ealegremendoza/proyecto_4to/docs/modulos/acc/acelerometro que consigio lucas.jpg

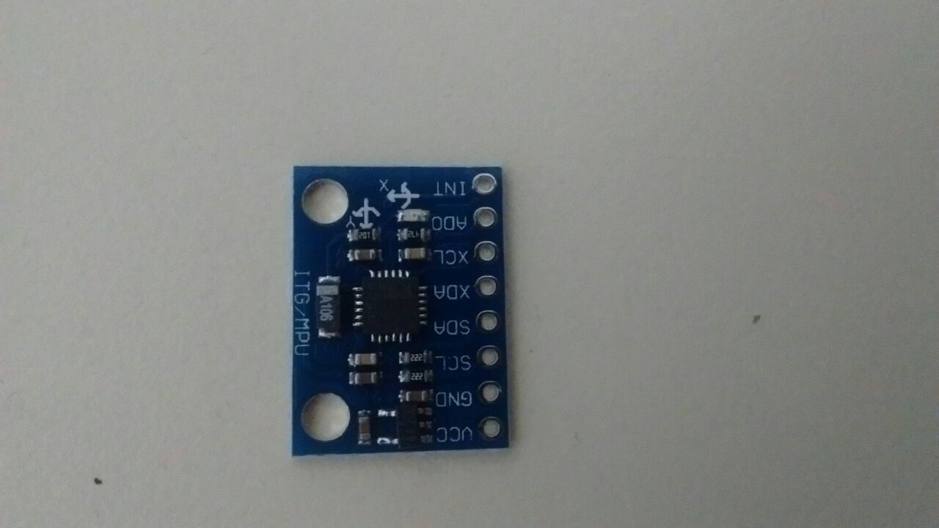
docs/modulos/acc/acelerometro que consigio lucas.jpg
