ealegremendoza/proyecto_4to/ezequiel/lpc1769_footprints.png

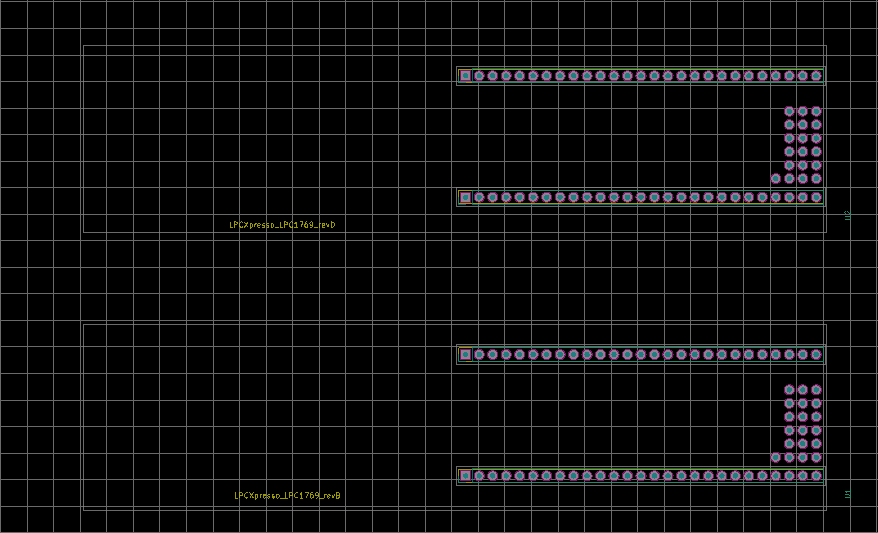
ezequiel/lpc1769_footprints.png
