ealegremendoza/proyecto_4to/docs/lpc_info/potencia_proyecto_lpc.ods

Periférico | Condición | Valor típico de suministro de corriente a 100MHz – [mA] | Notas | Vmax | Pmax | Cantidad | Pmaxtotal
Timer |  | 0,23 | Average current per timer |  | 0 | 2 | 0
UART |  | 0,53 | Average current per timer |  | 0 | 1 | 0
I2C |  | 0,16 | Average current per I2C | 0,7 | 0,112 | 1 | 0,112
SSP1 |  | 0,32 |  |  | 0 | 3 | 0
GPIO |  | 2,58 |  | 0,99 | 2,5542 | 10 | 25,542
PLL |  | CUANTO CONSUME? |  |  | #VALOR! | 1 | #VALOR!
