ealegremendoza/proyecto_4to/docs/gantt/gant_proy4to_planner_v1.pdf

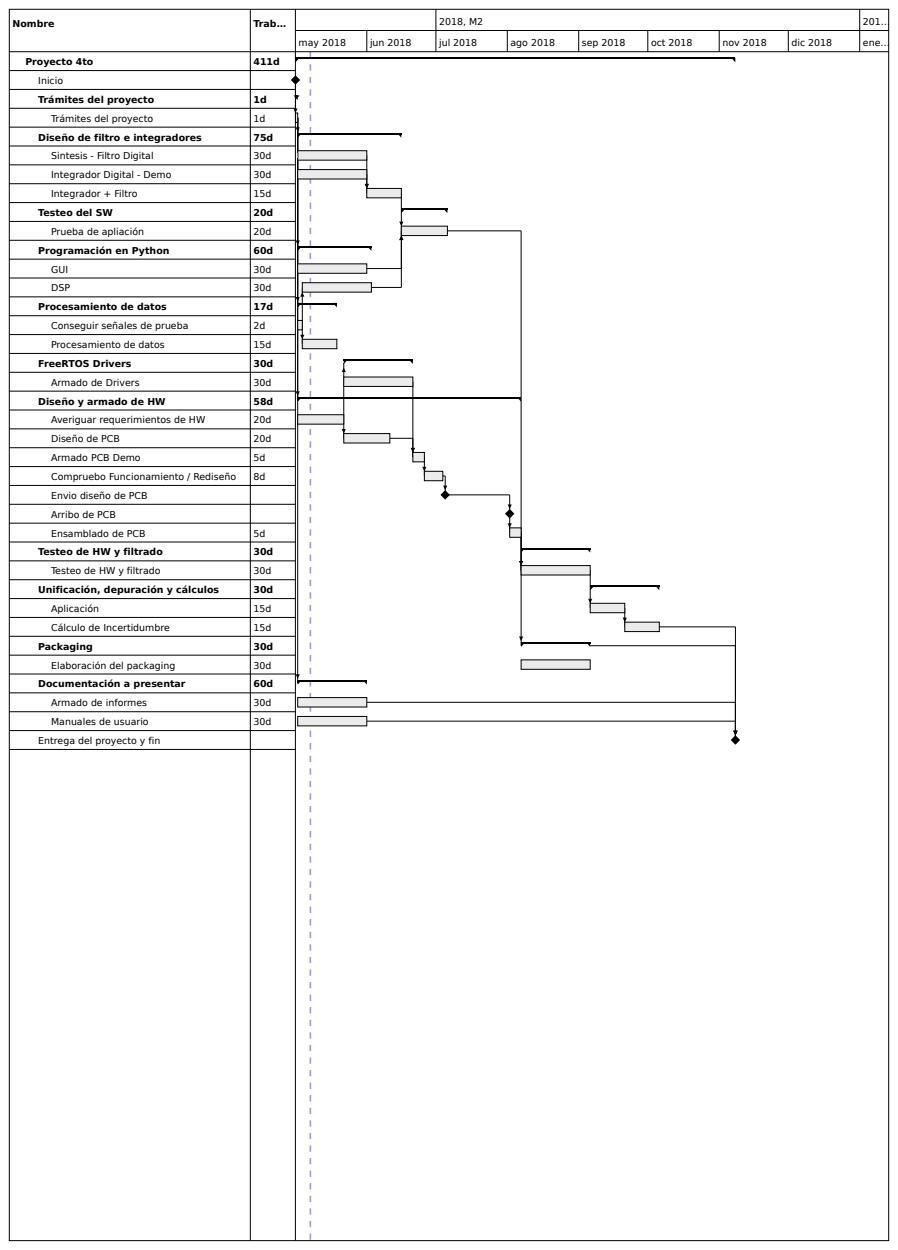
[picture p51: page 1]
Proyecto 4to; Trámites del proyecto; Diseño de filtro e integradores; Sintesis - Filtro Digital; Integrador Digital - Demo; Integrador + Filtro; Testeo del SW; Prueba de apliación; Programación en Python; GUI; DSP; Procesamiento de datos; Conseguir señales de prueba; FreeRTOS Drivers; Armado de Drivers; Diseño y armado de HW; Averiguar requerimientos de HW; Diseño de PCB; Armado PCB Demo; Compruebo Funcionamiento / Rediseño; Ensamblado de PCB; Testeo de HW y filtrado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

Inicio
Envio diseño de PCB
Arribo de PCB
Entrega del proyecto y fin

WBS | Nombre | Inicio | Fin | Trabajo | Duración | Desperdicio | Coste | Asignado a | % Completado
1 | Proyecto 4to | may 1 | nov 8 | 411d | 191d | | 0 | | 0
1.1 | Inicio | may 1 | may 1 | N/D | N/D | 62d | 0 | | 0
1.2 | Trámites del proyecto | may 1 | may 1 | 1d | 22h 58min | 190d | 0 | | 0
1.2.1 | Trámites del proyecto | may 1 | may 1 | 1d | 1d | 62d | 0 | | 0
1.3 | Diseño de filtro e integradores | may 1 | jun 15 | 75d | 45d | 145d | 0 | | 0
1.3.1 | Sintesis - Filtro Digital | may 1 | may 31 | 30d | 30d | 65d | 0 | | 2
1.3.2 | Integrador Digital - Demo | may 1 | may 31 | 30d | 30d | 65d | 0 | | 0
1.3.3 | Integrador + Filtro | may 31 | jun 15 | 15d | 15d | 65d | 0 | | 0
1.4 | Testeo del SW | jun 15 | jul 5 | 20d | 20d | 125d | 0 | | 0
1.4.1 | Prueba de apliación | jun 15 | jul 5 | 20d | 20d | 65d | 0 | | 0
1.5 | Programación en Python | may 1 | jun 2 | 60d | 32d | 158d | 0 | | 0
1.5.1 | GUI | may 1 | may 31 | 30d | 30d | 80d | 0 | | 0
1.5.2 | DSP | may 3 | jun 2 | 30d | 30d | 78d | 0 | | 0
1.6 | Procesamiento de datos | may 1 | may 18 | 17d | 17d | 173d | 0 | | 0
1.6.1 | Conseguir señales de prueba | may 1 | may 3 | 2d | 2d | 78d | 0 | | 0
1.6.2 | Procesamiento de datos | may 3 | may 18 | 15d | 15d | 173d | 0 | | 0
1.7 | FreeRTOS Drivers | may 21 | jun 20 | 30d | 30d | 140d | 0 | | 0
1.7.1 | Armado de Drivers | may 21 | jun 20 | 30d | 30d | 62d | 0 | | 0
1.8 | Diseño y armado de HW | may 1 | ago 6 | 58d | 97d | 93d | 0 | | 0
1.8.1 | Averiguar requerimientos de HW | may 1 | may 21 | 20d | 20d | 62d | 0 | | 0
1.8.2 | Diseño de PCB | may 21 | jun 10 | 20d | 20d | 72d | 0 | | 0
1.8.3 | Armado PCB Demo | jun 20 | jun 25 | 5d | 5d | 62d | 0 | | 0
1.8.4 | Compruebo Funcionamiento / Rediseño | jun 25 | jul 3 | 8d | 8d | 62d | 0 | | 0
1.8.5 | Envio diseño de PCB | jul 5 | jul 5 | N/D | N/D | 61d | 0 | | 0
1.8.6 | Arribo de PCB | ago 2 | ago 2 | N/D | N/D | 33d | 0 | | 0
1.8.7 | Ensamblado de PCB | ago 2 | ago 6 | 5d | 5d | 33d | 0 | | 0
1.9 | Testeo de HW y filtrado | ago 6 | sep 5 | 30d | 30d | 63d | 0 | | 0
1.9.1 | Testeo de HW y filtrado | ago 6 | sep 5 | 30d | 30d | 33d | 0 | | 0
1.10 | Unificación, depuración y cálculos | sep 5 | oct 5 | 30d | 30d | 33d | 0 | | 0
1.10.1 | Aplicación | sep 5 | sep 20 | 15d | 15d | 33d | 0 | | 0
1.10.2 | Cálculo de Incertidumbre | sep 20 | oct 5 | 15d | 15d | 33d | 0 | | 0
1.11 | Packaging | ago 6 | sep 5 | 30d | 30d | 63d | 0 | | 0
1.11.1 | Elaboración del packaging | ago 6 | sep 5 | 30d | 30d | 63d | 0 | | 0
1.12 | Documentación a presentar | may 1 | may 31 | 60d | 30d | 160d | 0 | | 0
1.12.1 | Armado de informes | may 1 | may 31 | 30d | 30d | 160d | 0 | | 0
1.12.2 | Manuales de usuario | may 1 | may 31 | 30d | 30d | 160d | 0 | | 0
1.13 | Entrega del proyecto y fin | nov 8 | nov 8 | N/D | N/D | | 0 | | 0
