ealegremendoza/proyecto_4to/pcbs/cargador/pdf/cargador_pcb_1.pdf

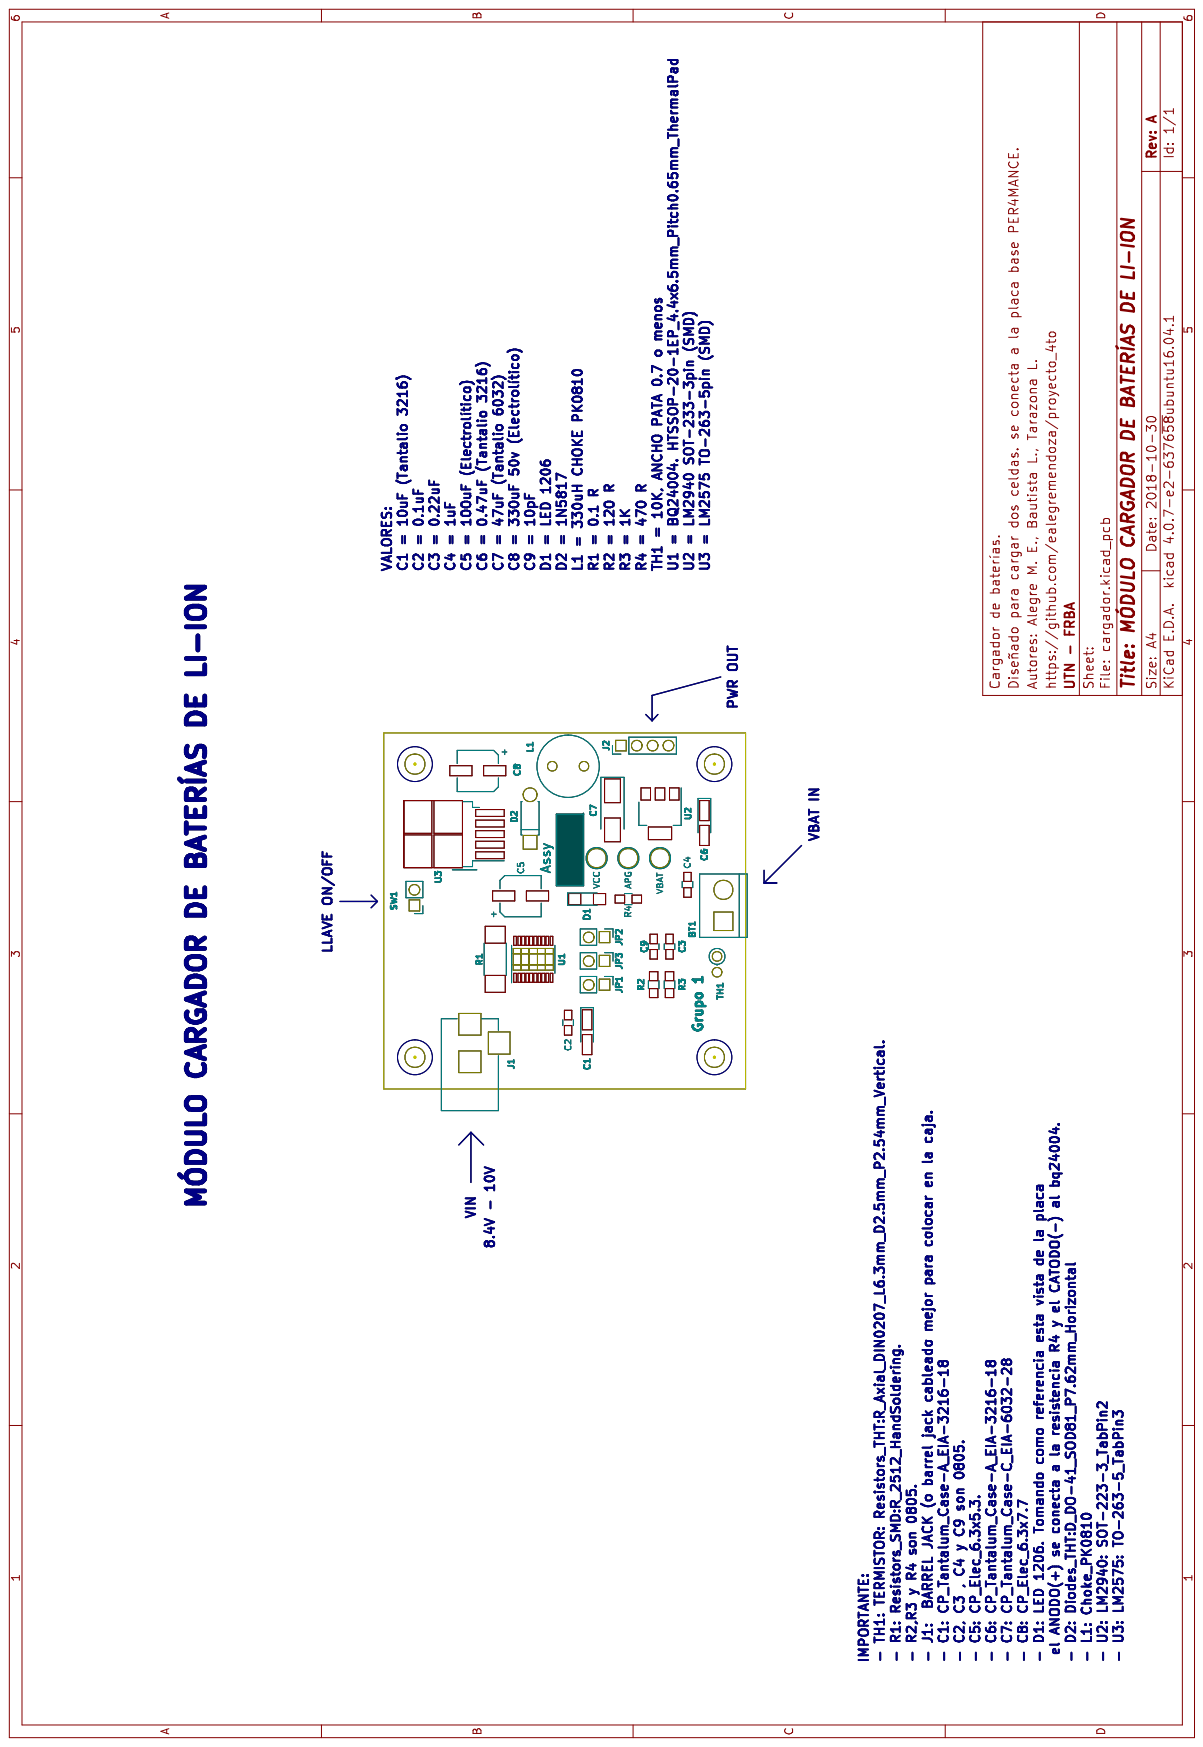
[picture p52: page 1]
