ealegremendoza/proyecto_4to/pcbs/cargador/pdf/cargador_pcb_bottom.pdf

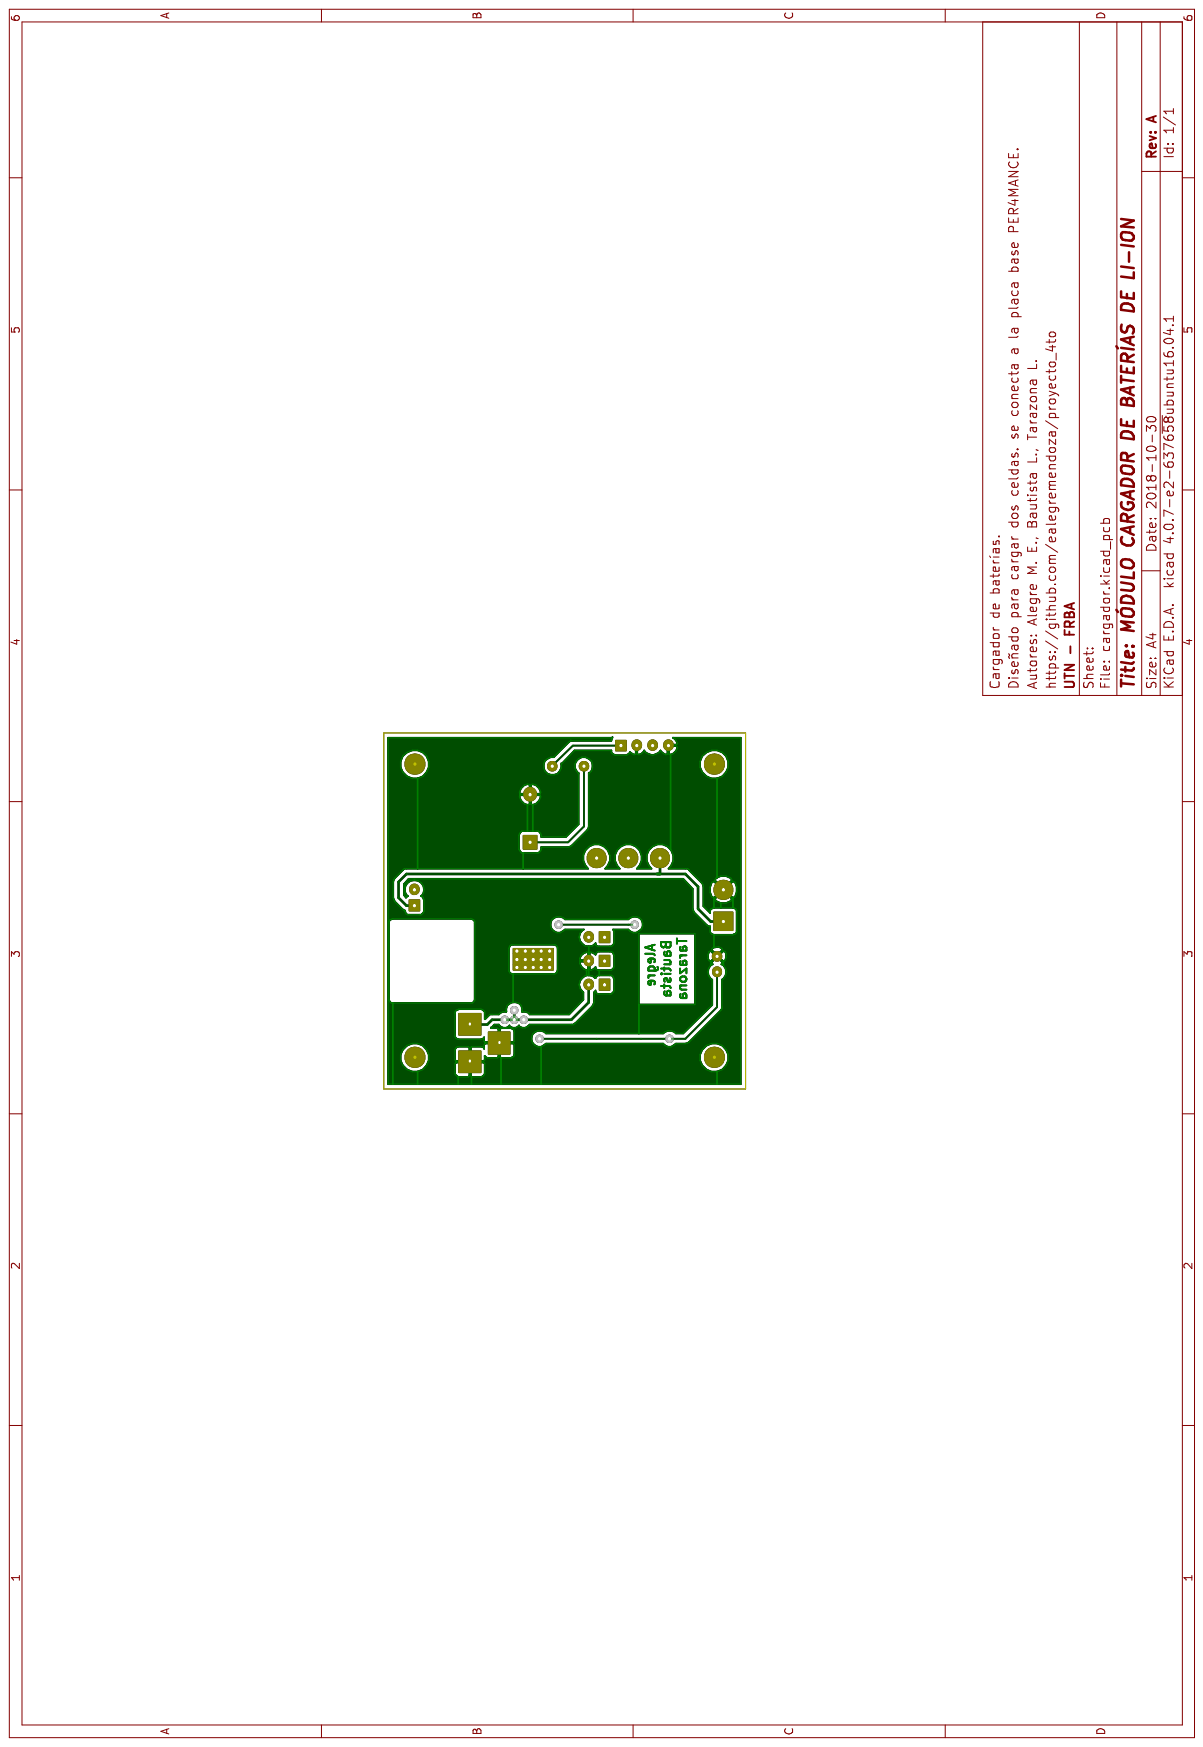
[picture p53: page 1]
