ealegremendoza/proyecto_4to/pcbs/cargador/pdf/cargador_pcb_dimensiones.pdf

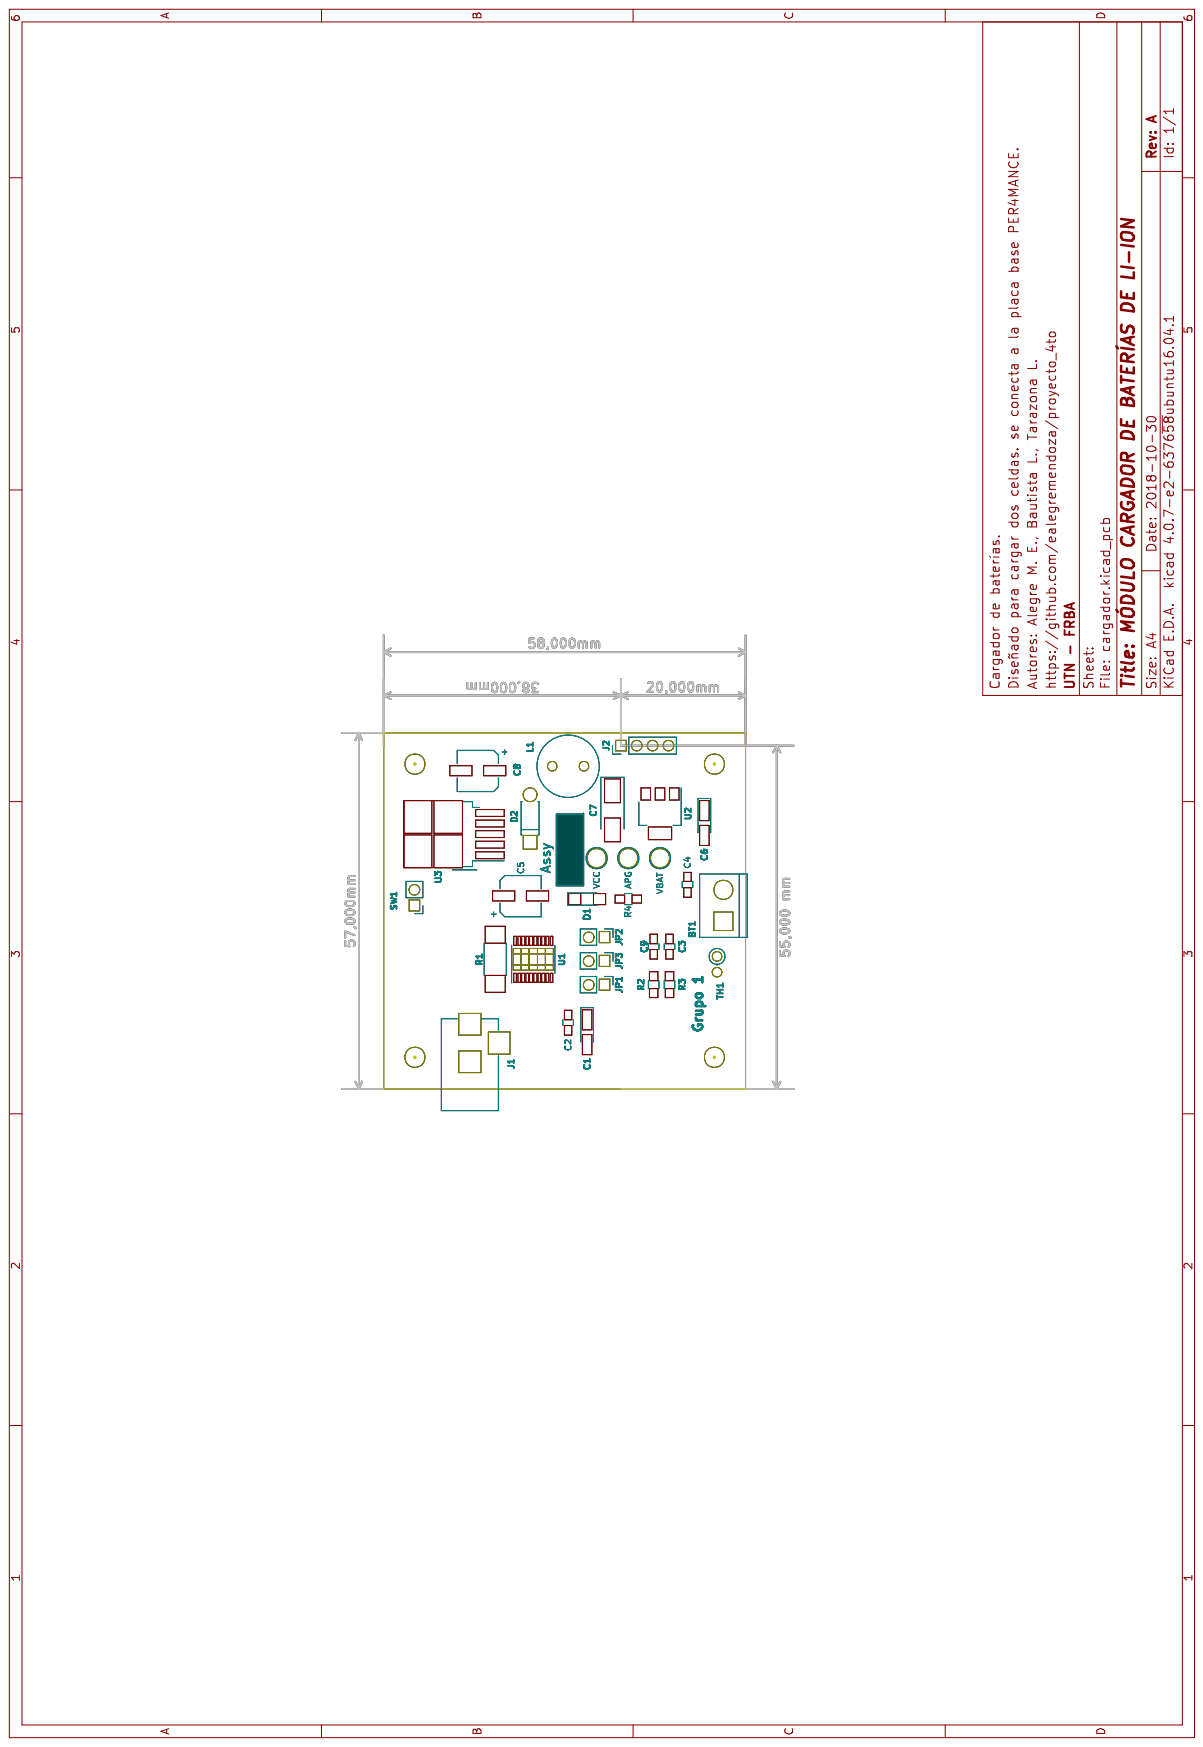
[picture p54: page 1]
