ealegremendoza/proyecto_4to/pcbs/cargador/pdf/cargador_pcb_top.pdf

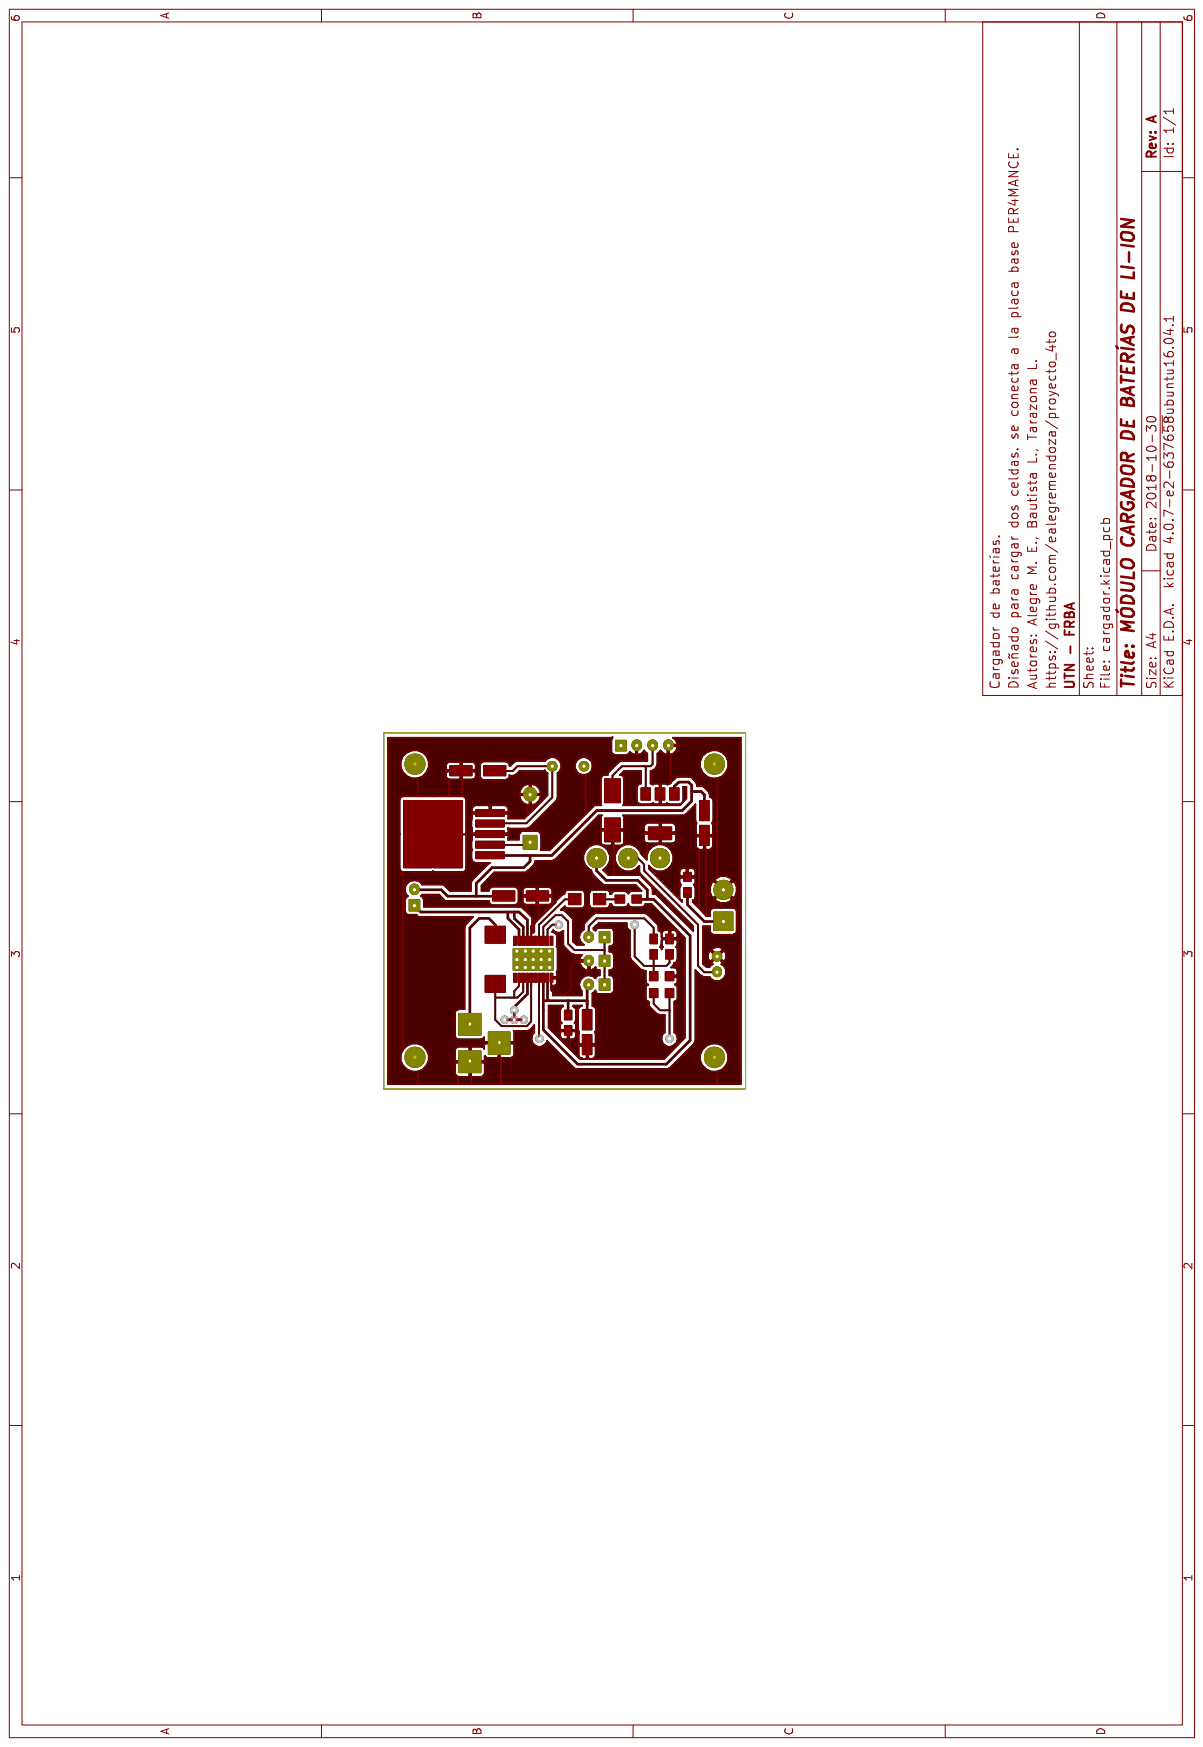
[picture p55: page 1]
