ealegremendoza/proyecto_4to/pcbs/pbase-ino/pdf/pbase-ino_pcb_1.pdf

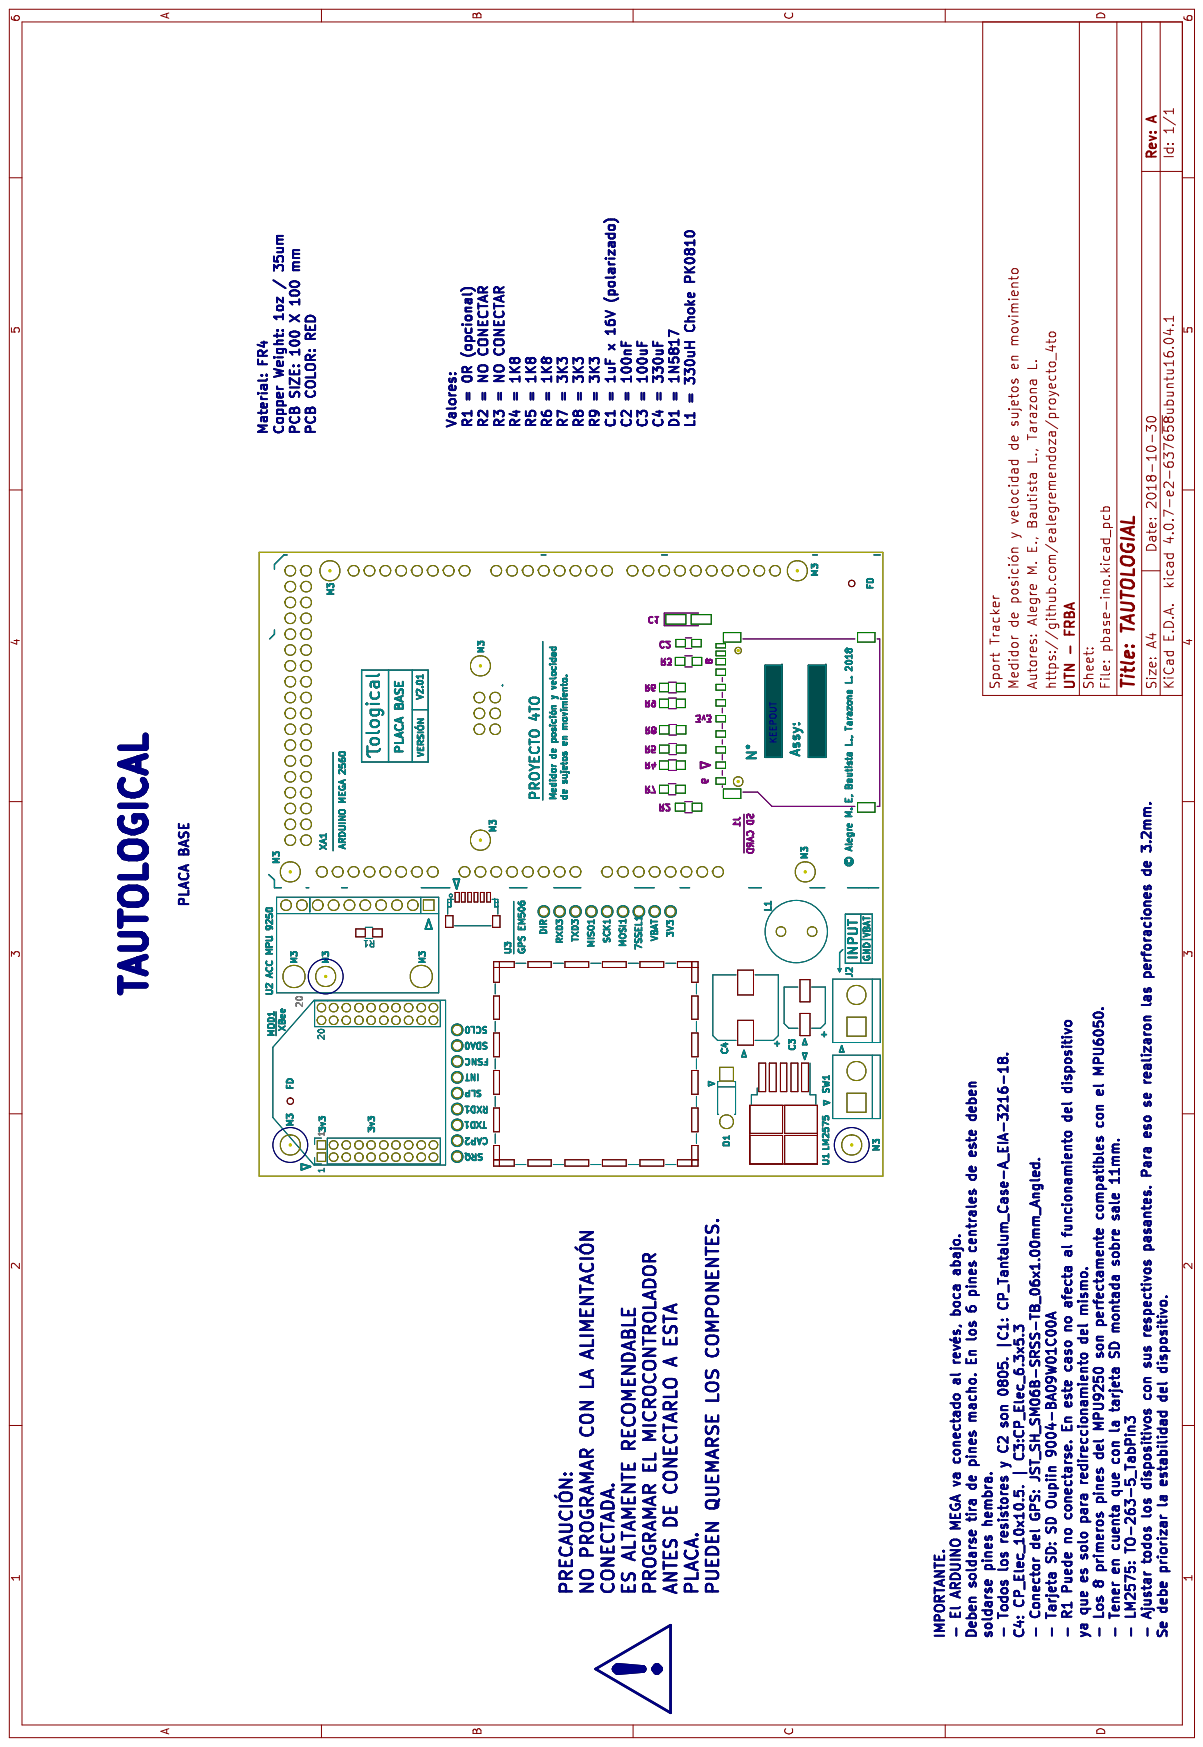
[picture p56: page 1]
