ealegremendoza/proyecto_4to/pcbs/pbase-ino/pdf/pbase-ino_pcb_bottom.pdf

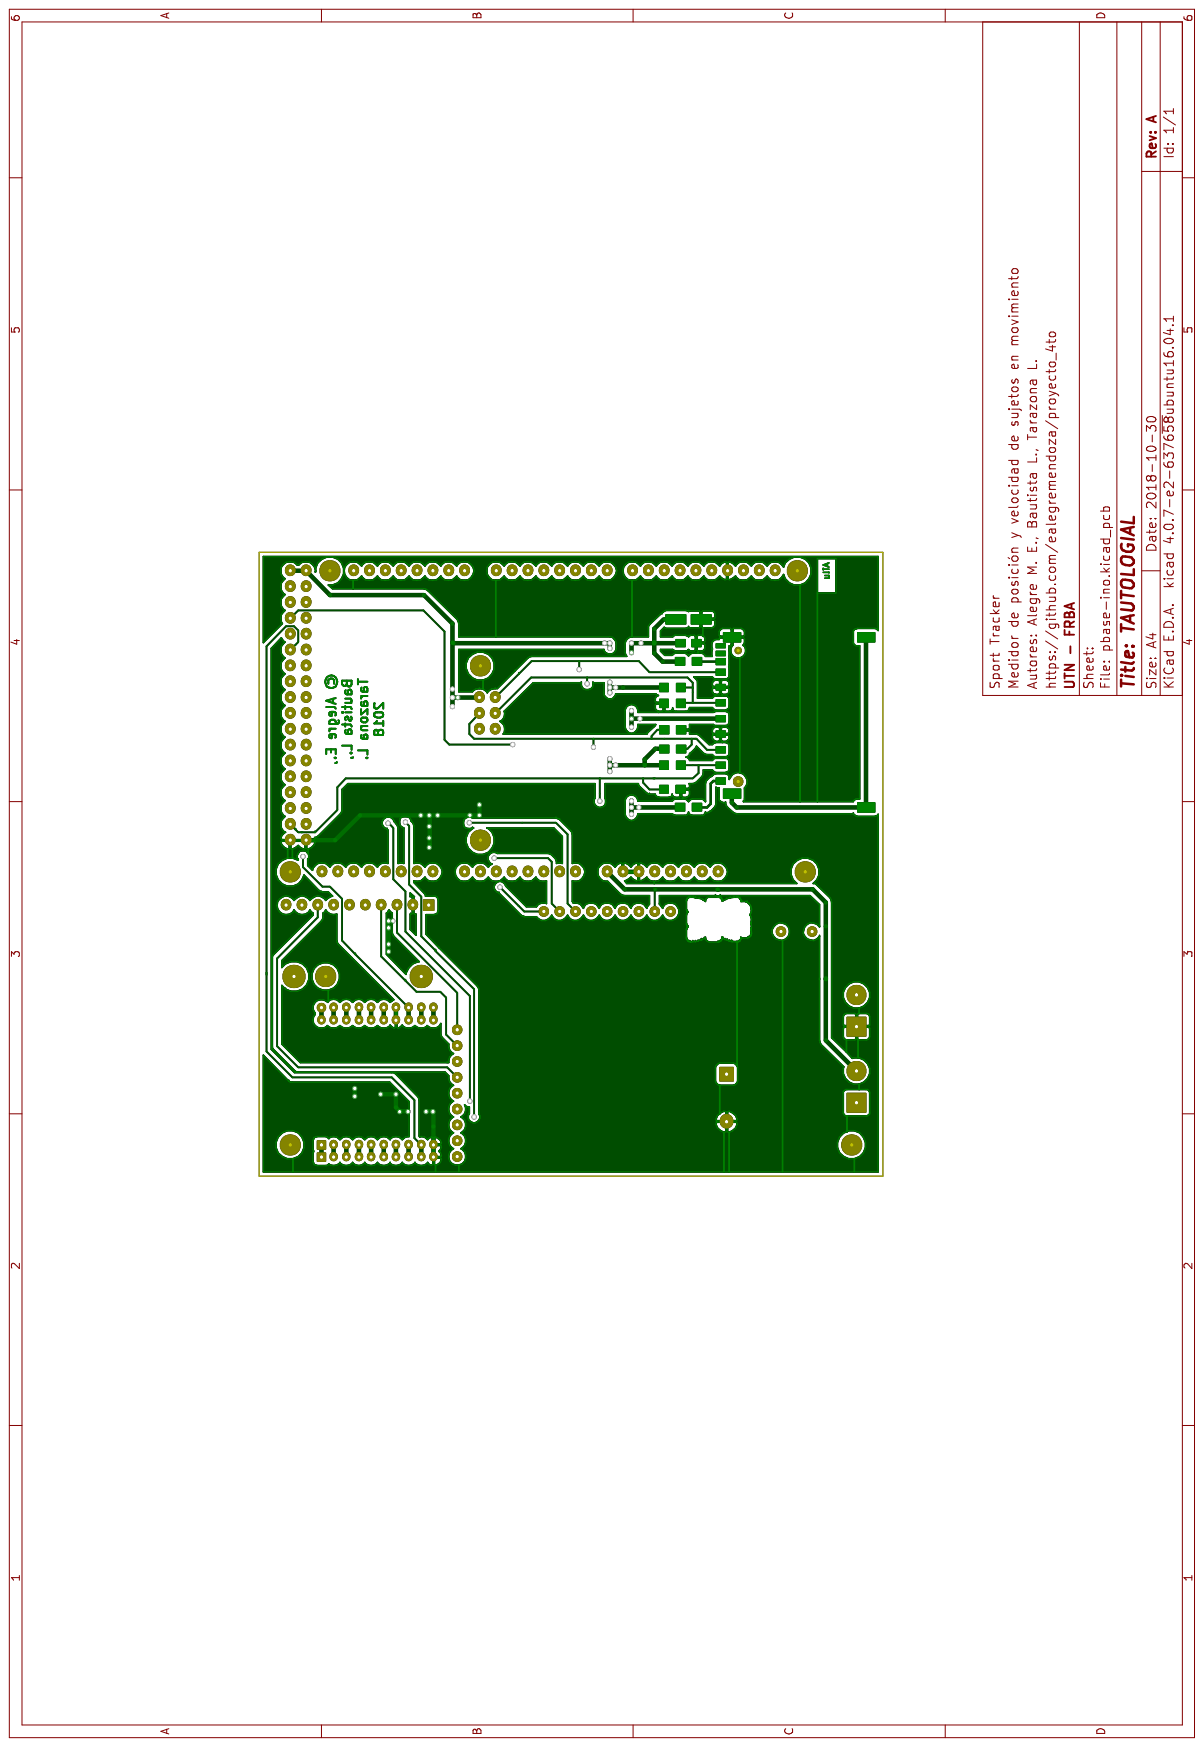
[picture p57: page 1]
