ealegremendoza/proyecto_4to/pcbs/pbase-ino/pdf/pbase-ino_pcb_dimensiones.pdf

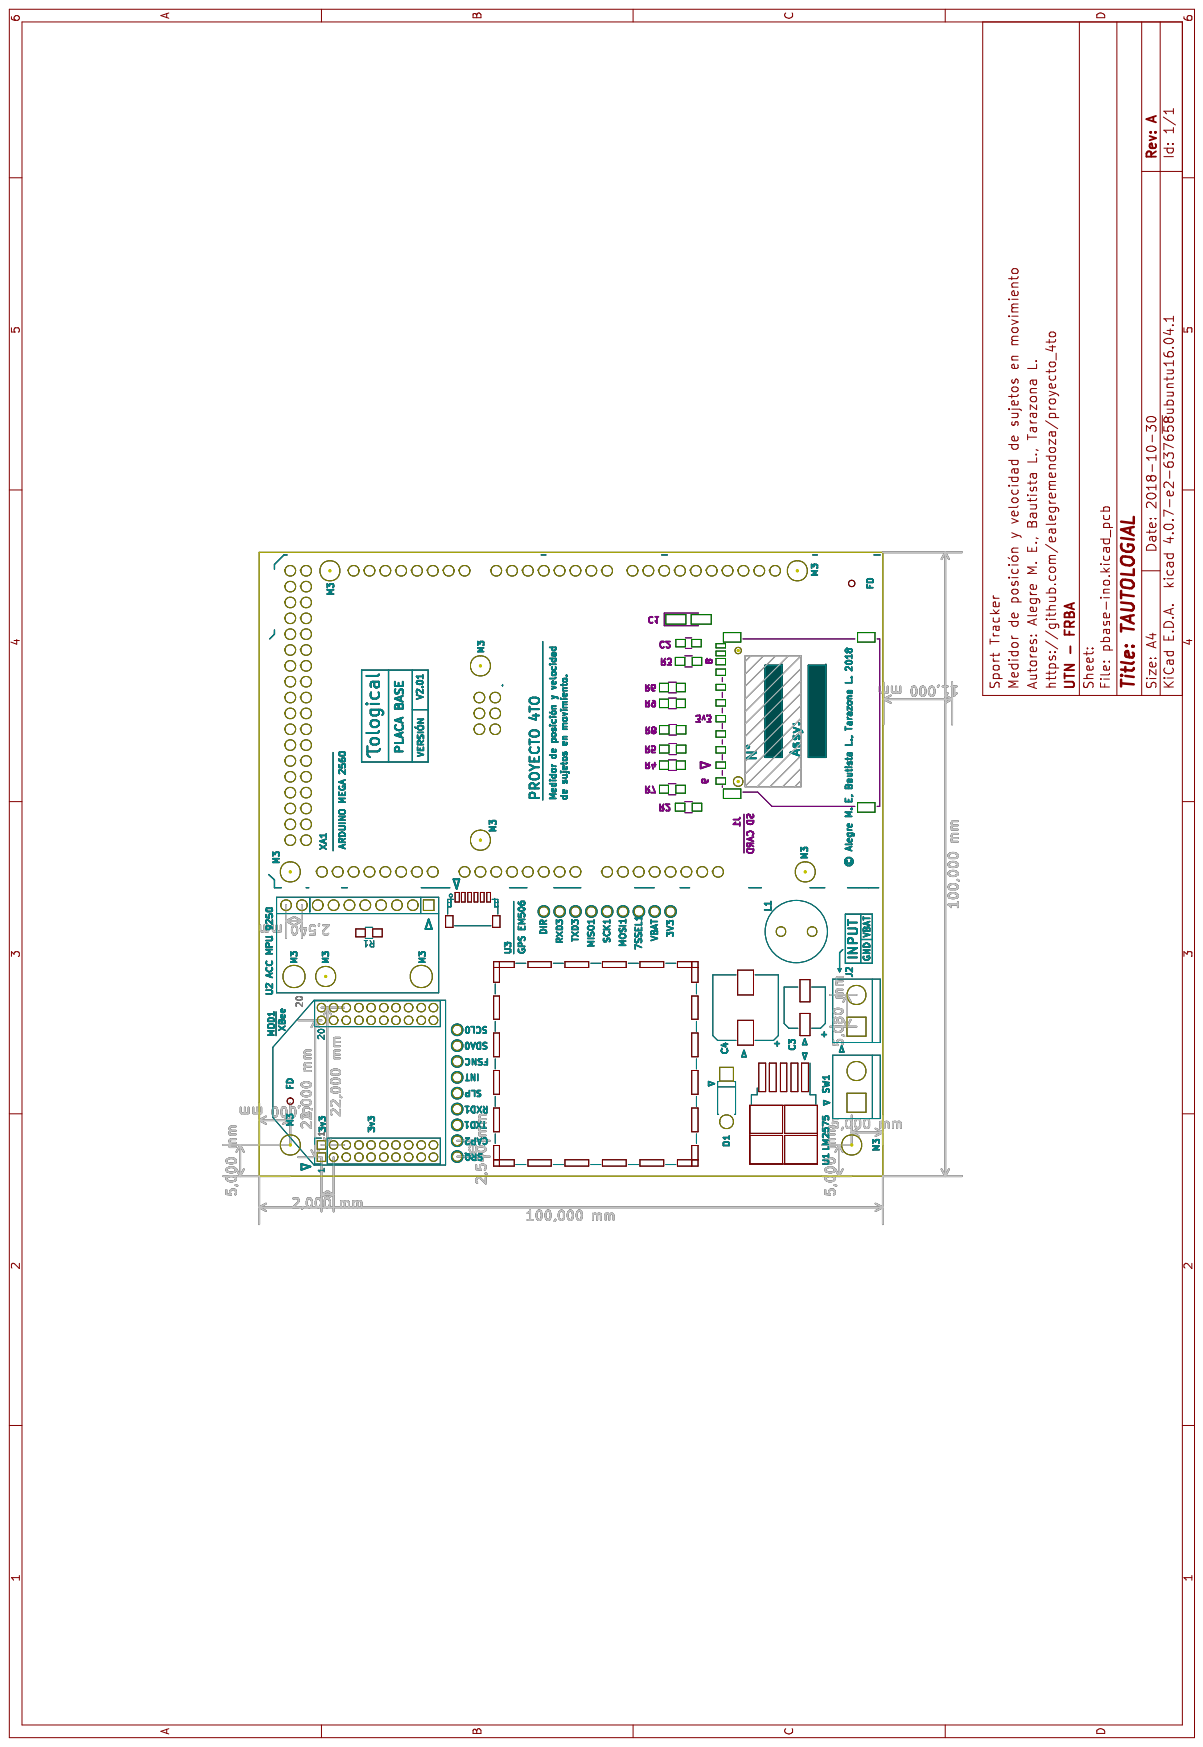
[picture p58: page 1]
