ealegremendoza/proyecto_4to/pcbs/pbase-ino/pdf/pbase-ino_pcb_front.pdf

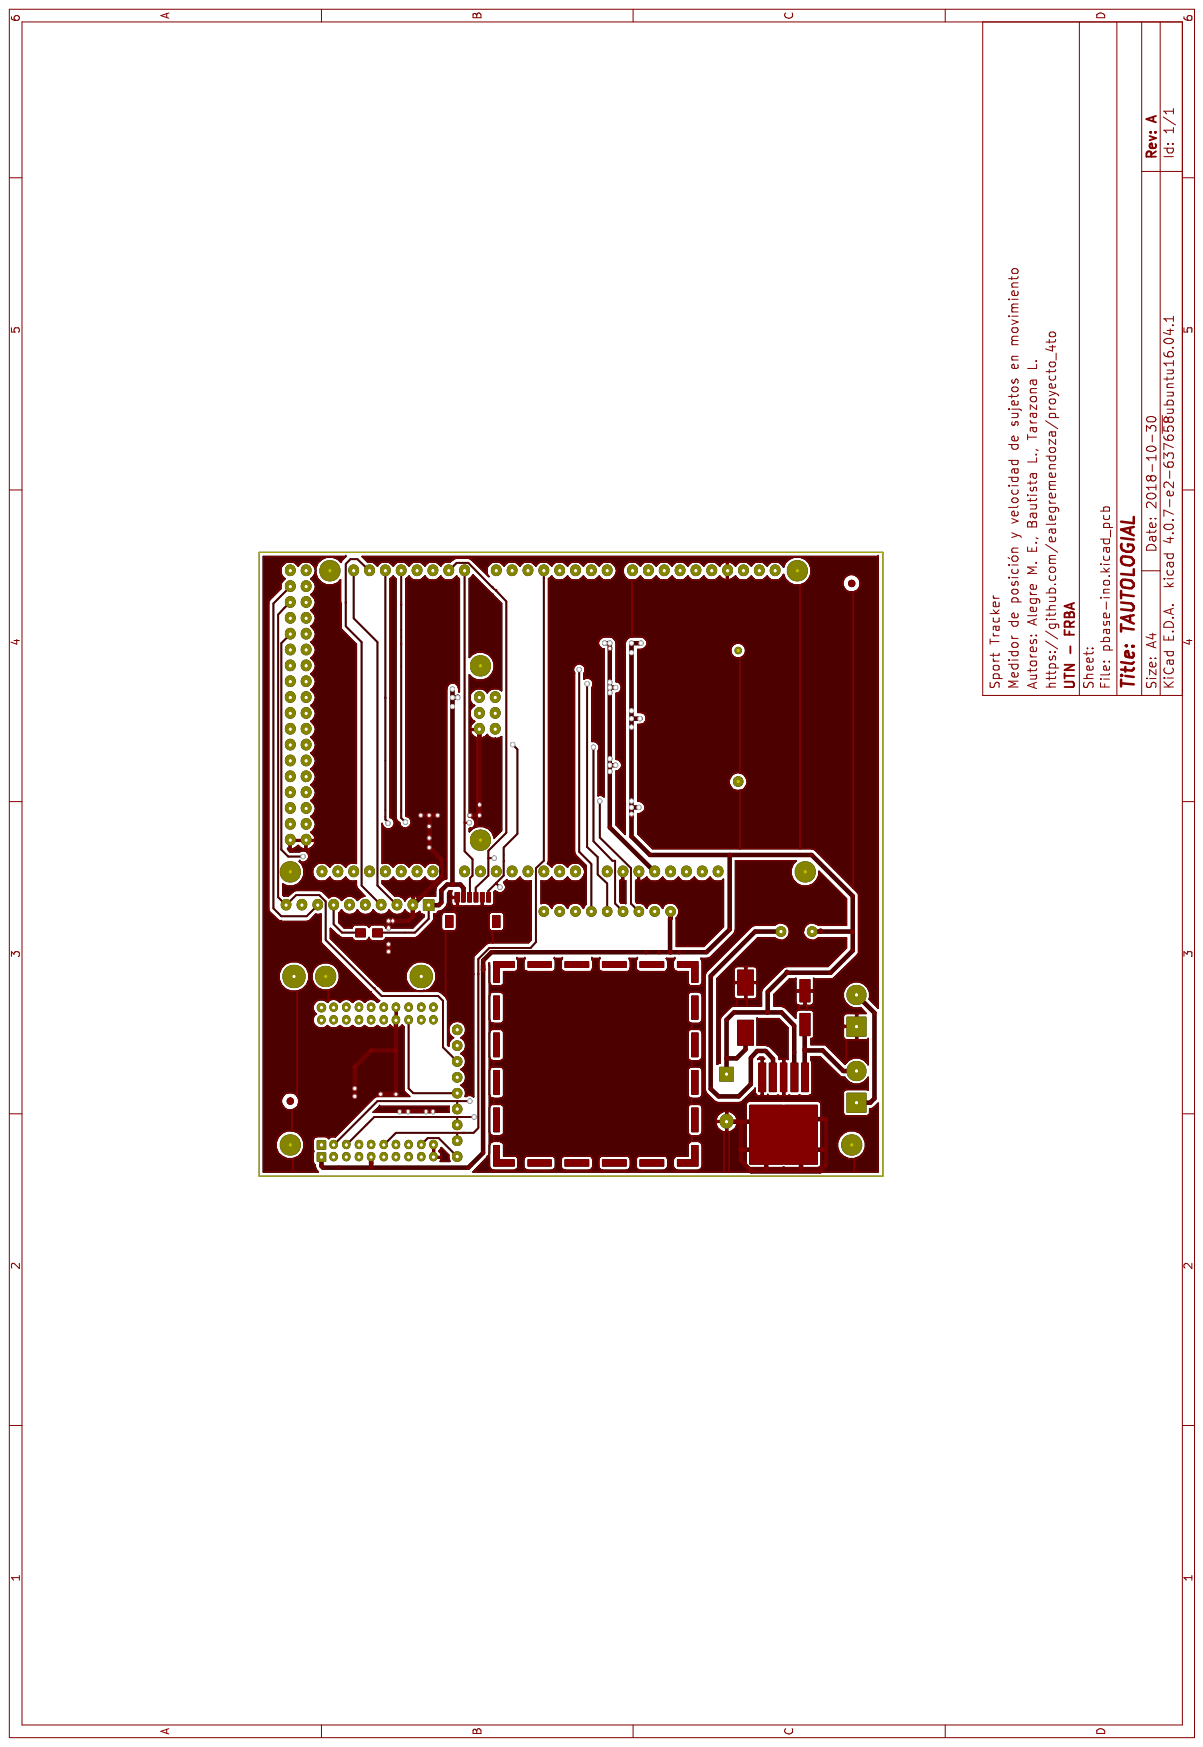
[picture p59: page 1]
