ealegremendoza/proyecto_4to/pcbs/pbase/pdf/pbase_pcb_1.pdf

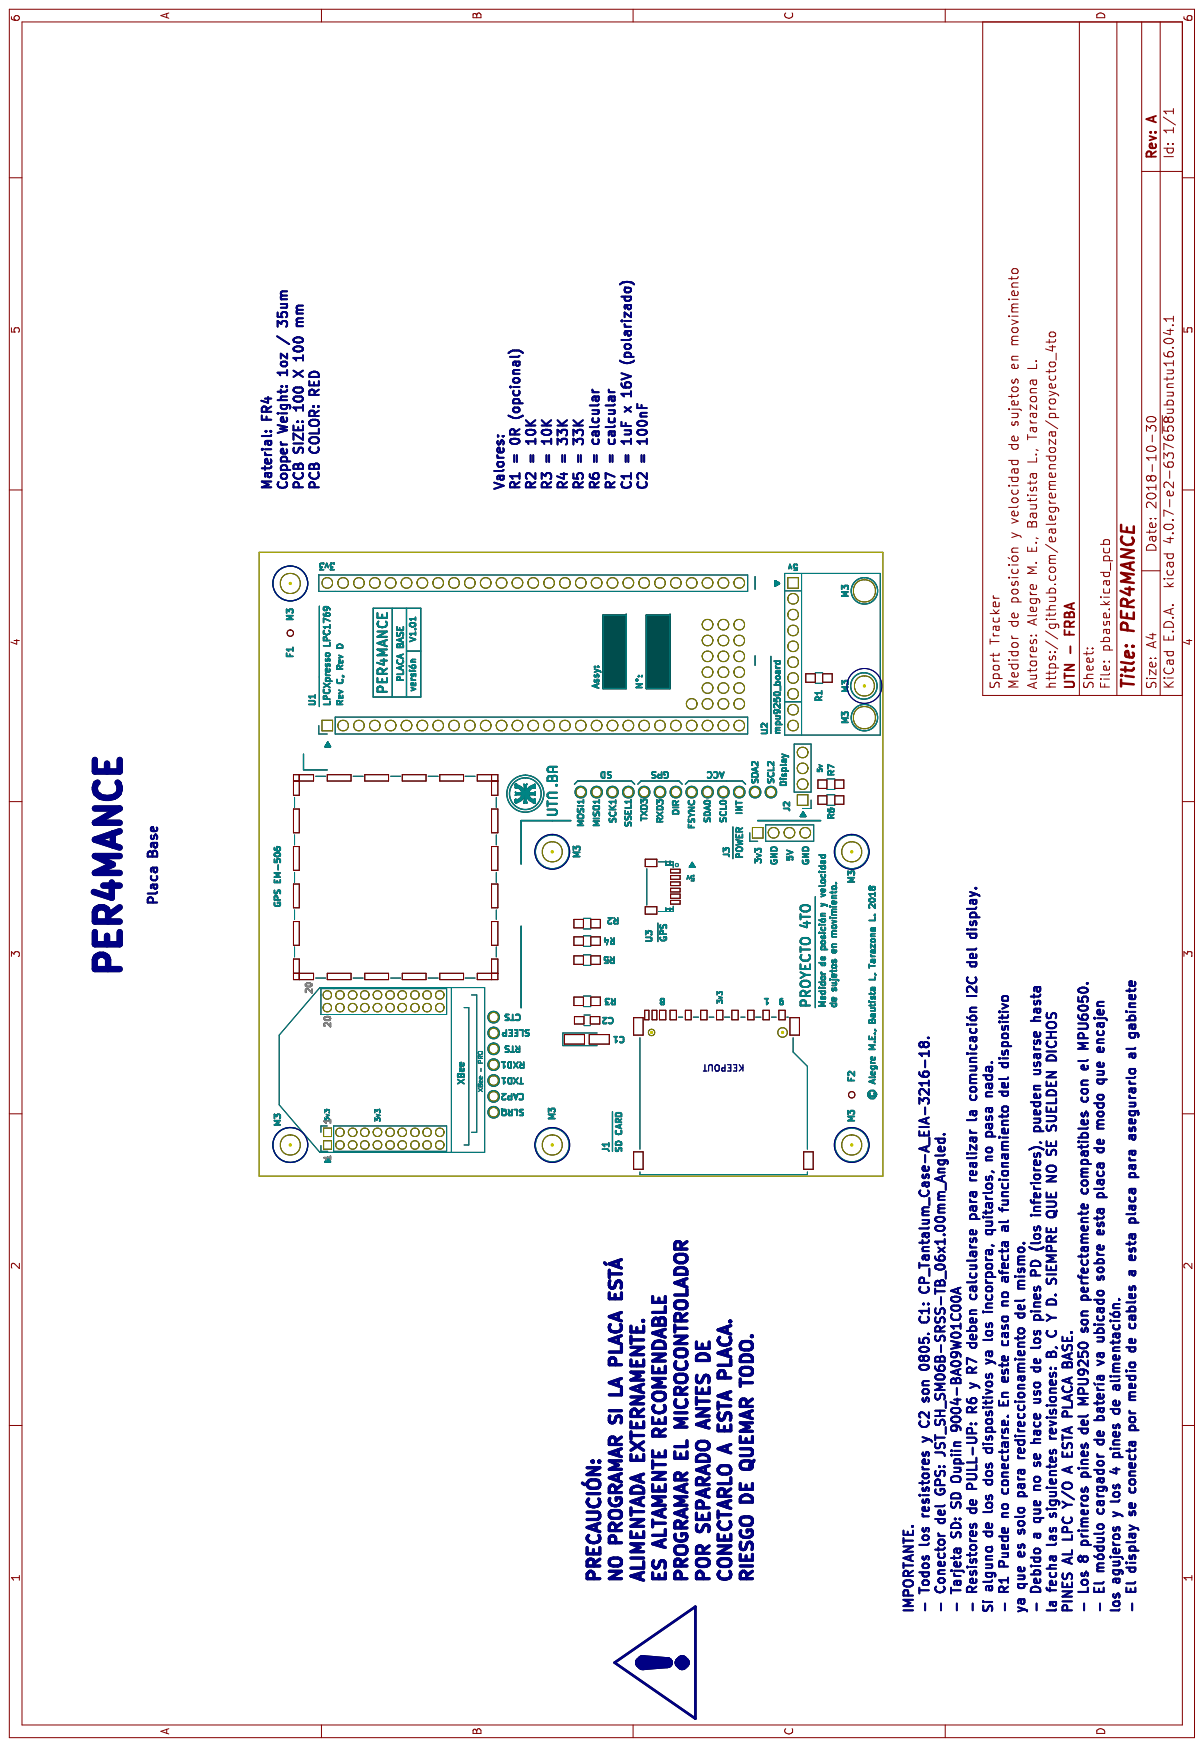
[picture p60: page 1]
