ealegremendoza/proyecto_4to/pcbs/pbase/pdf/pbase_pcb_bottom.pdf

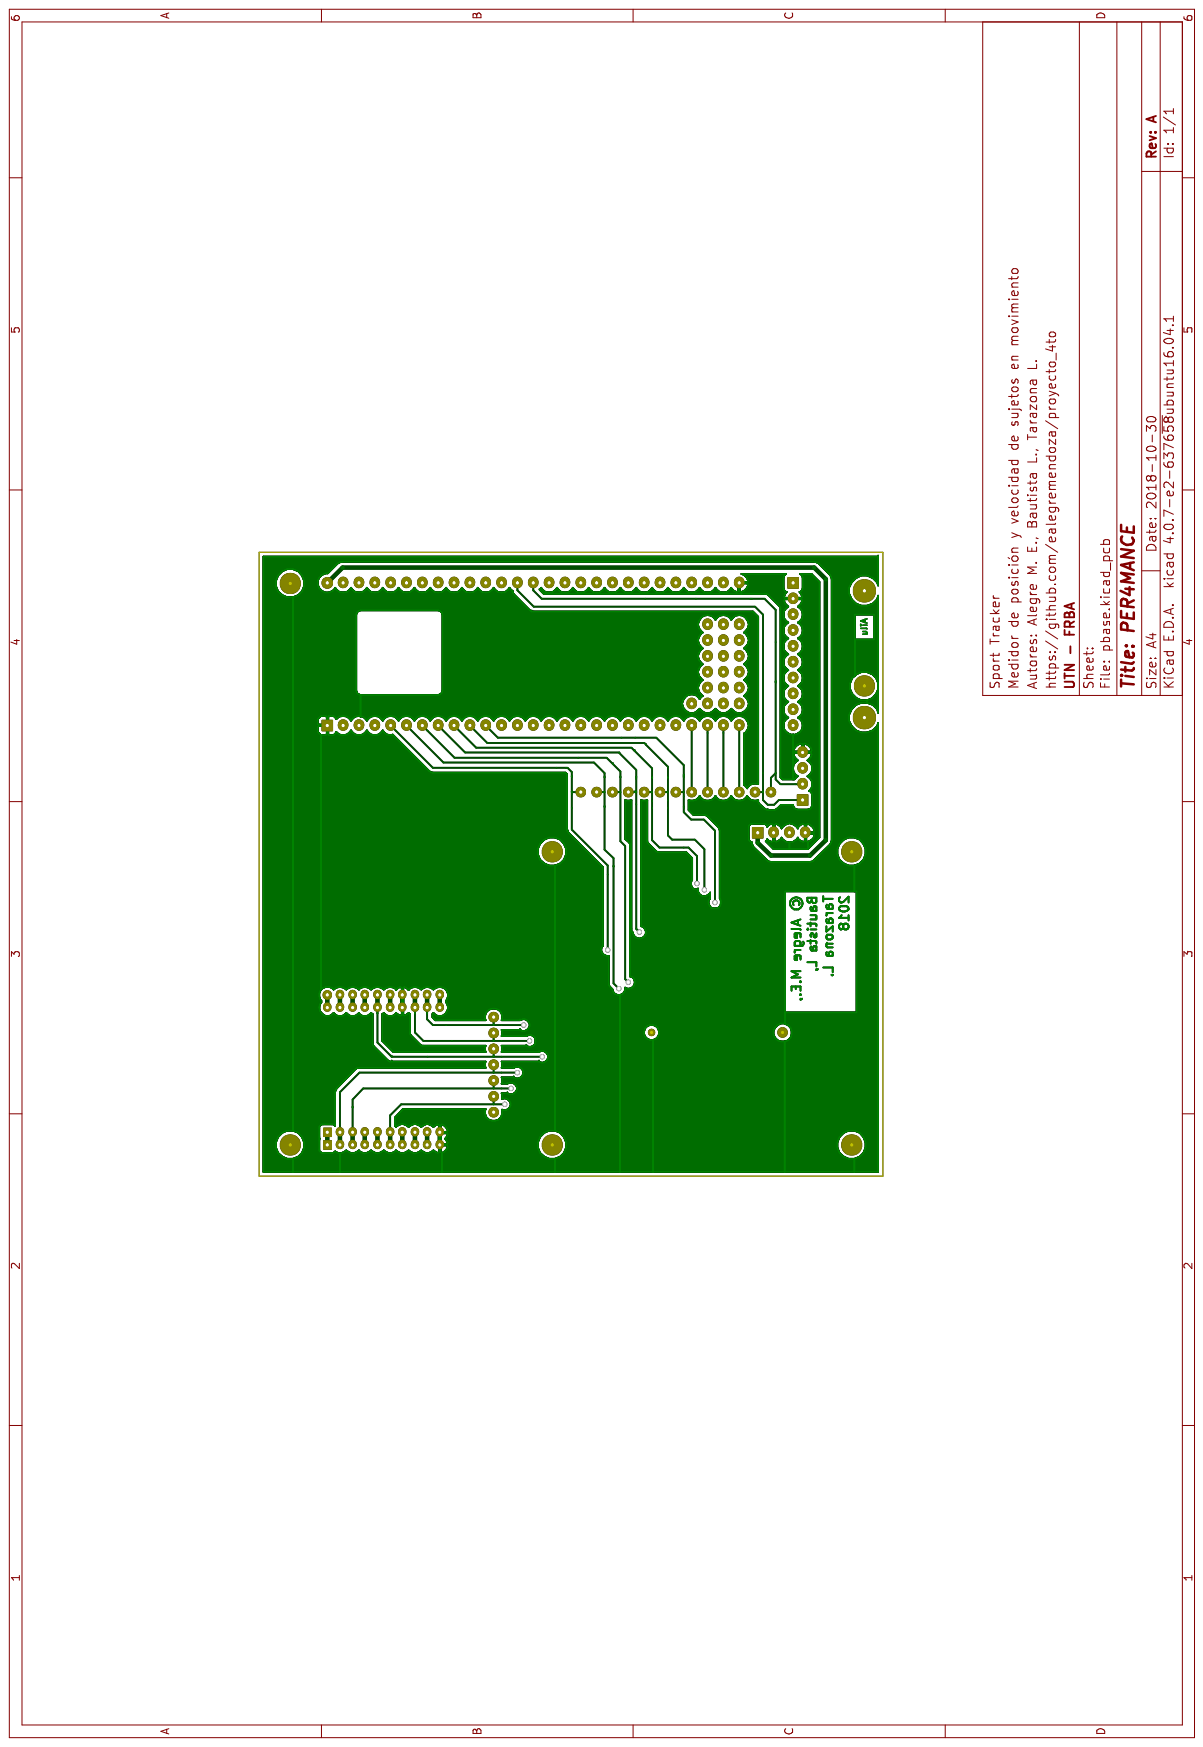
[picture p61: page 1]
