ealegremendoza/proyecto_4to/pcbs/pbase/pdf/pbase_pcb_dimensiones.pdf

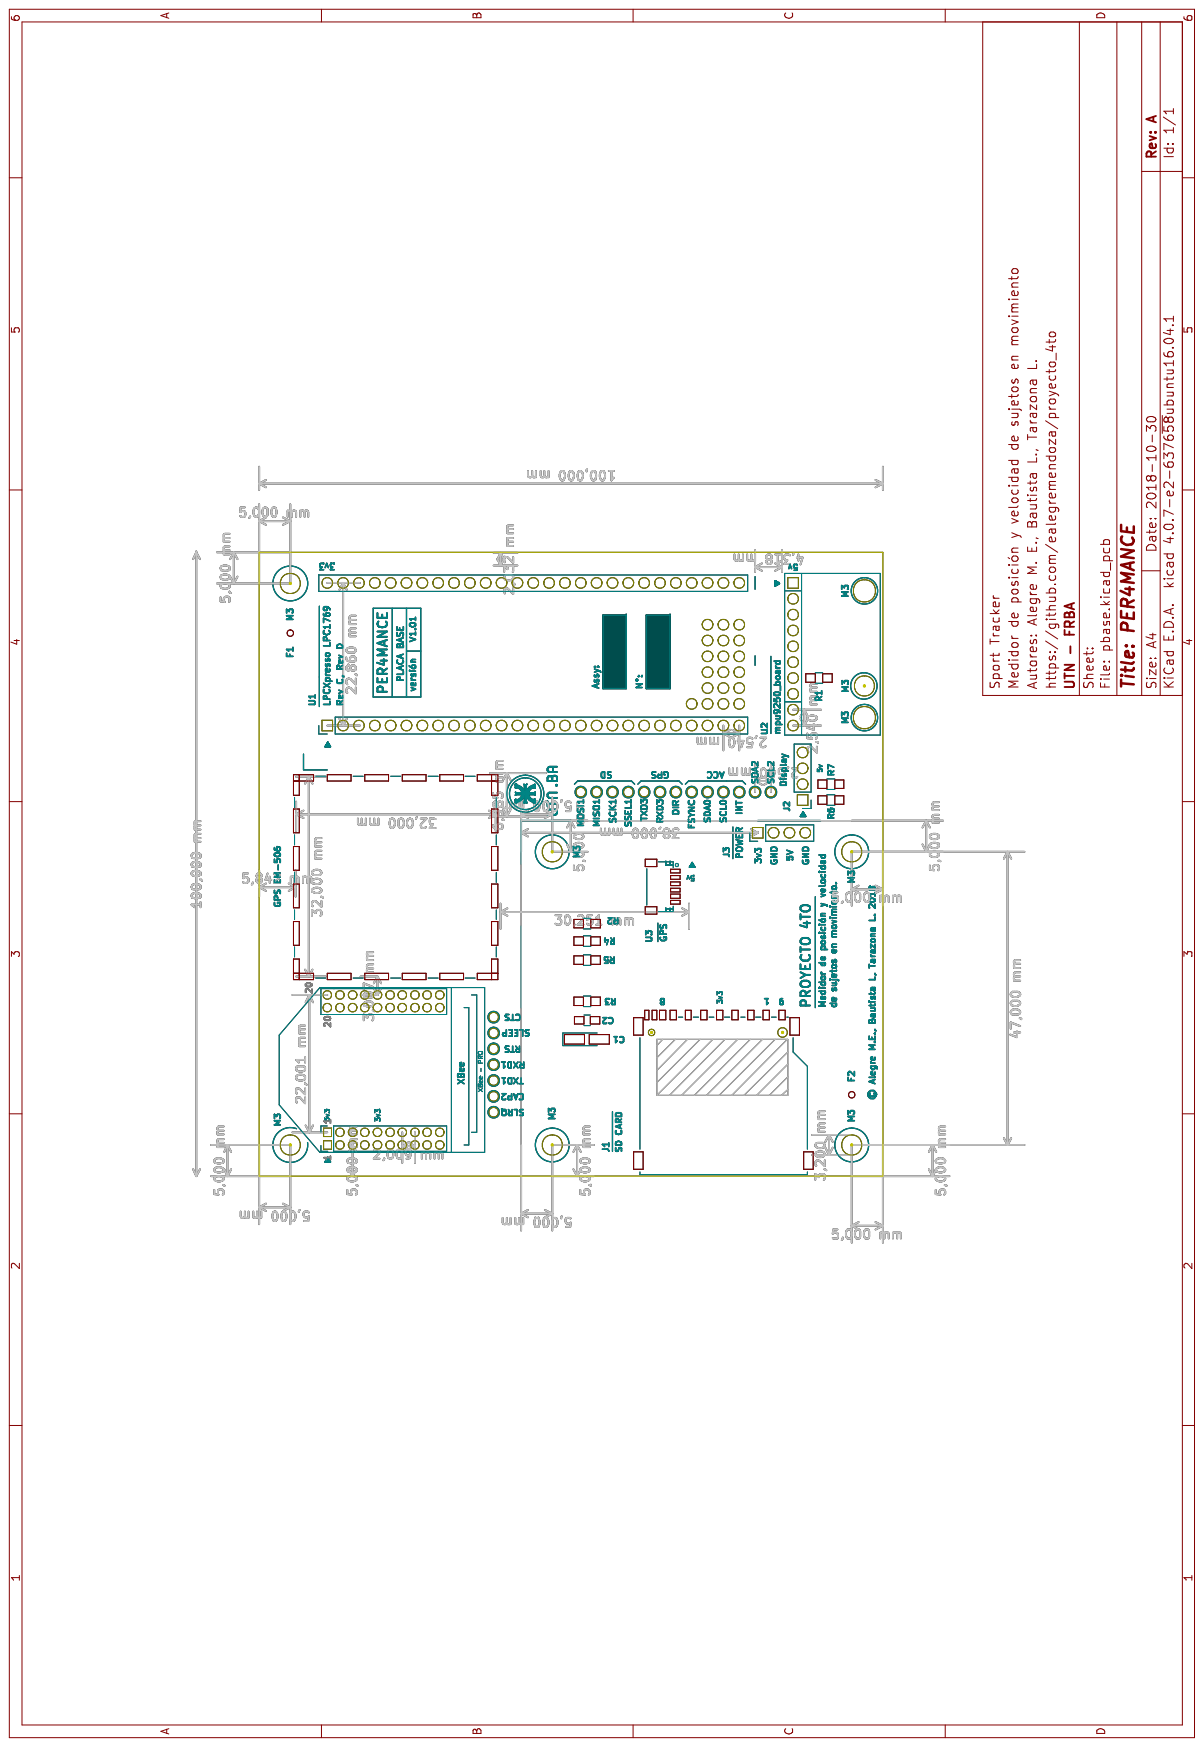
[picture p62: page 1]
