ealegremendoza/proyecto_4to/pcbs/pbase/pdf/pbase_pcb_front.pdf

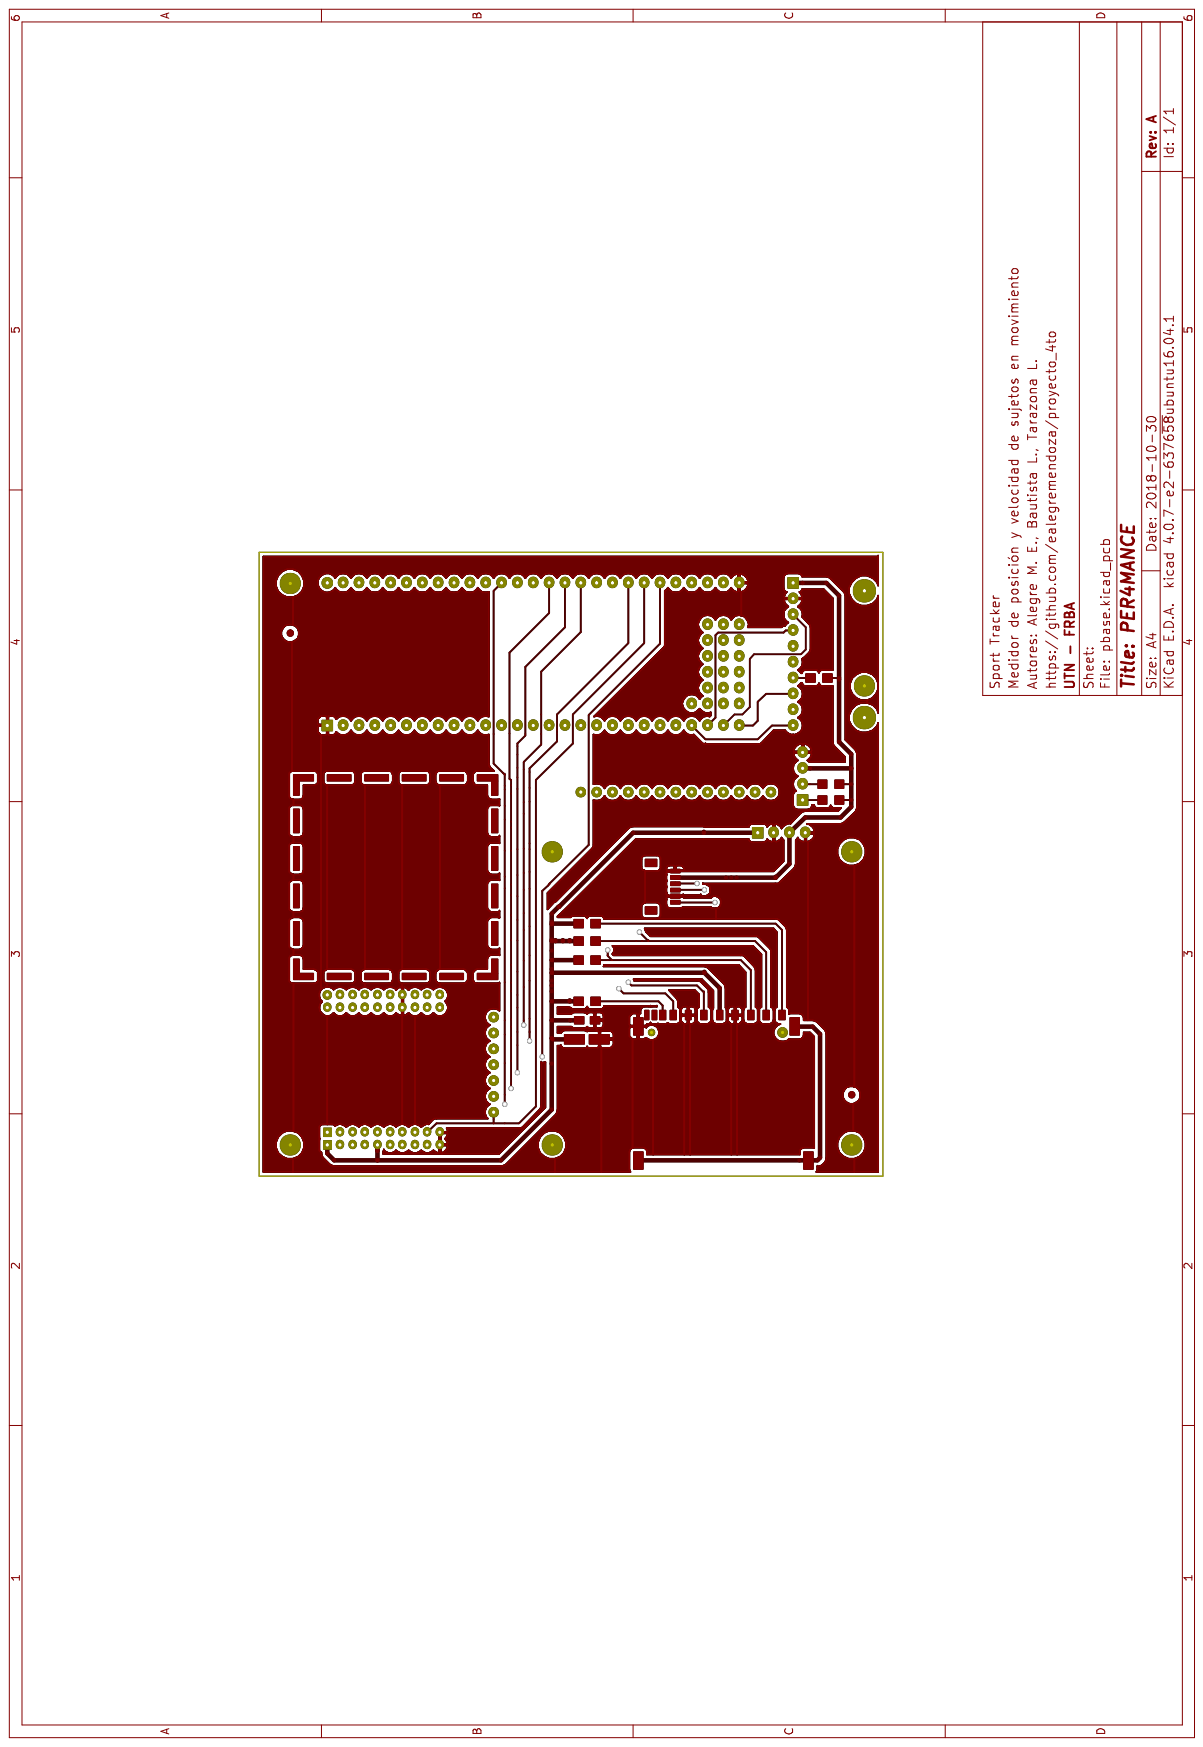
[picture p63: page 1]
