ealegremendoza/proyecto_4to/pcbs/pbase-ino_planchable/pdf/BOTTOM.pdf

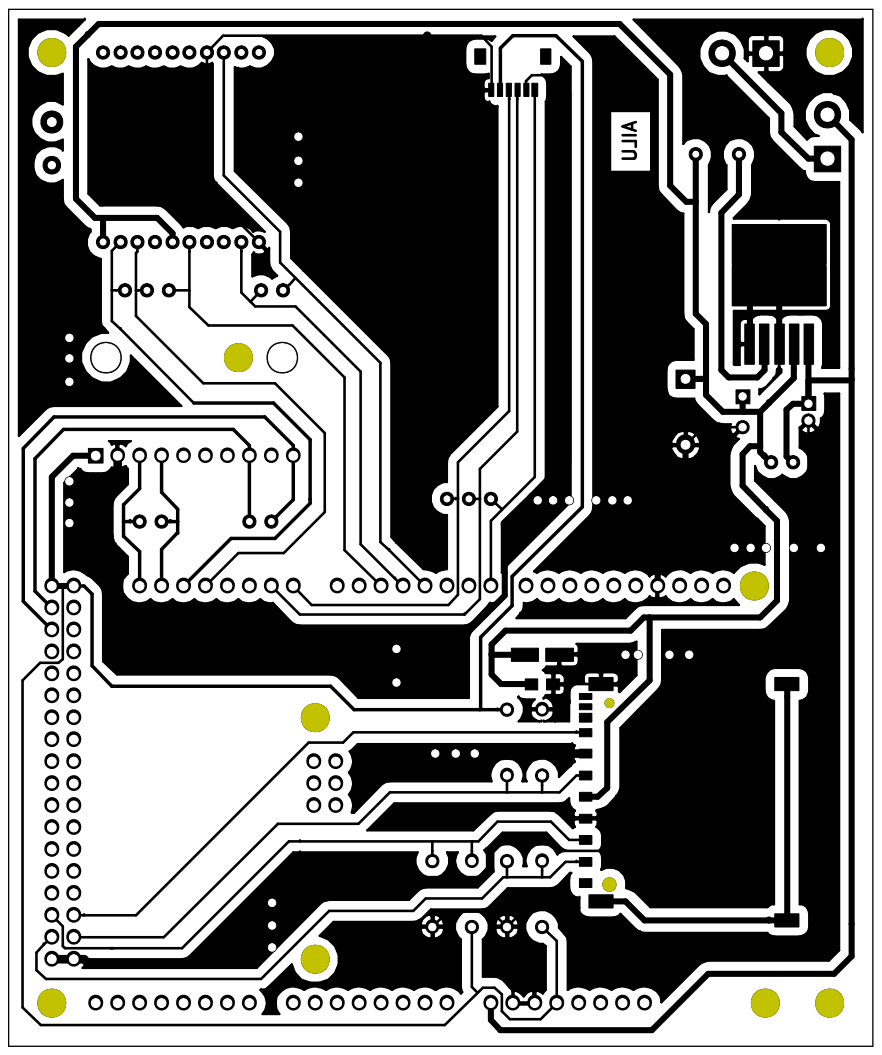
[picture p64: page 1]
