ealegremendoza/proyecto_4to/pcbs/pbase-ino_planchable/pdf/FRONT.pdf

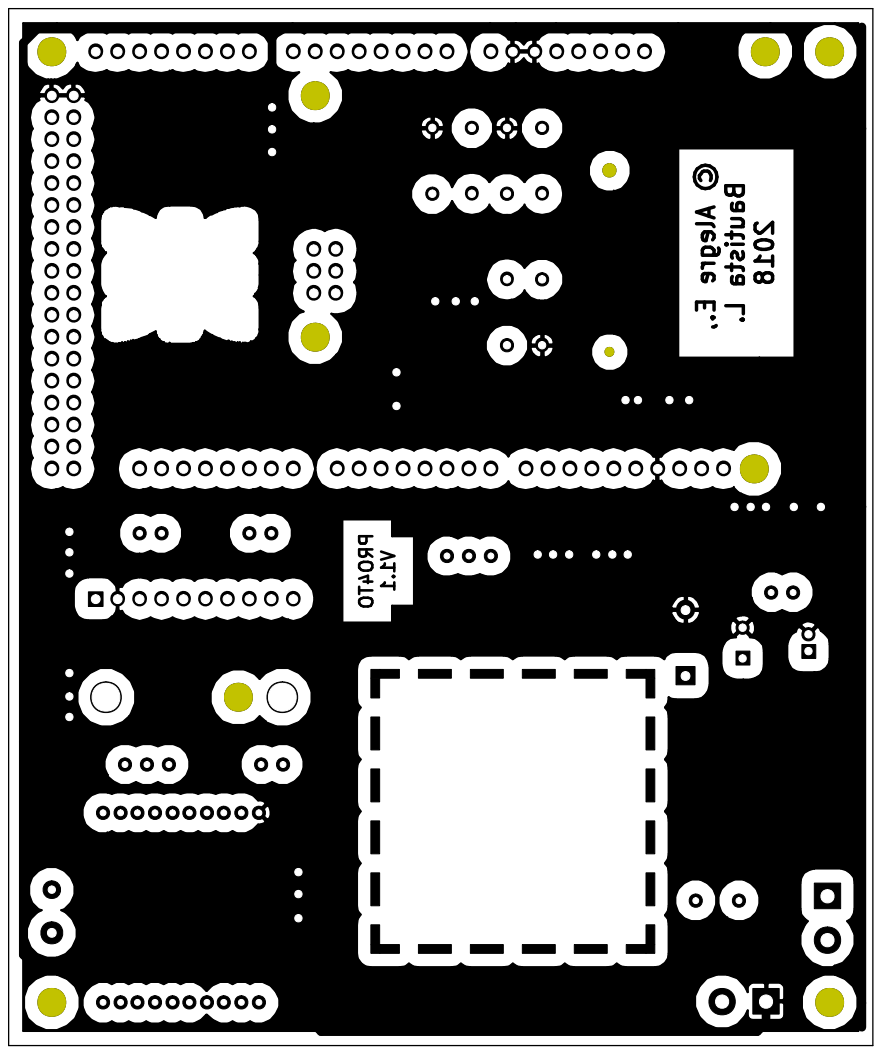
[picture p65: page 1]
