ealegremendoza/proyecto_4to/pcbs/pbase-ino_planchable/pdf/pbase-ino_planchable.pdf

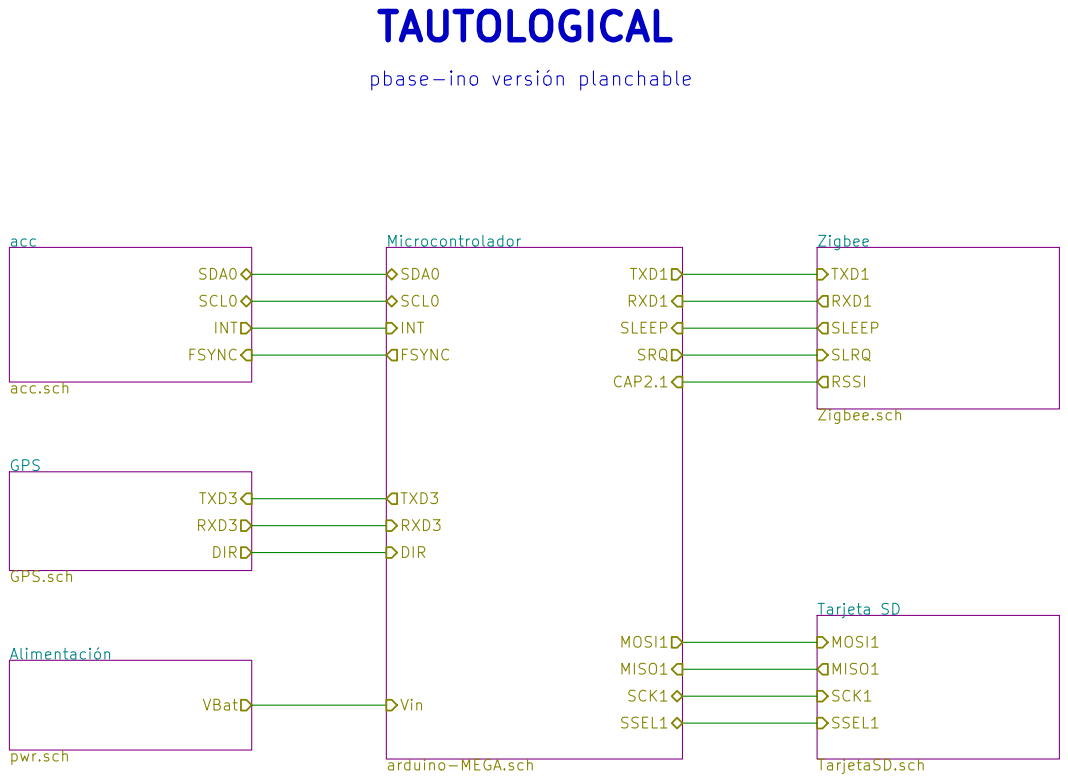
[picture p66: page 1]

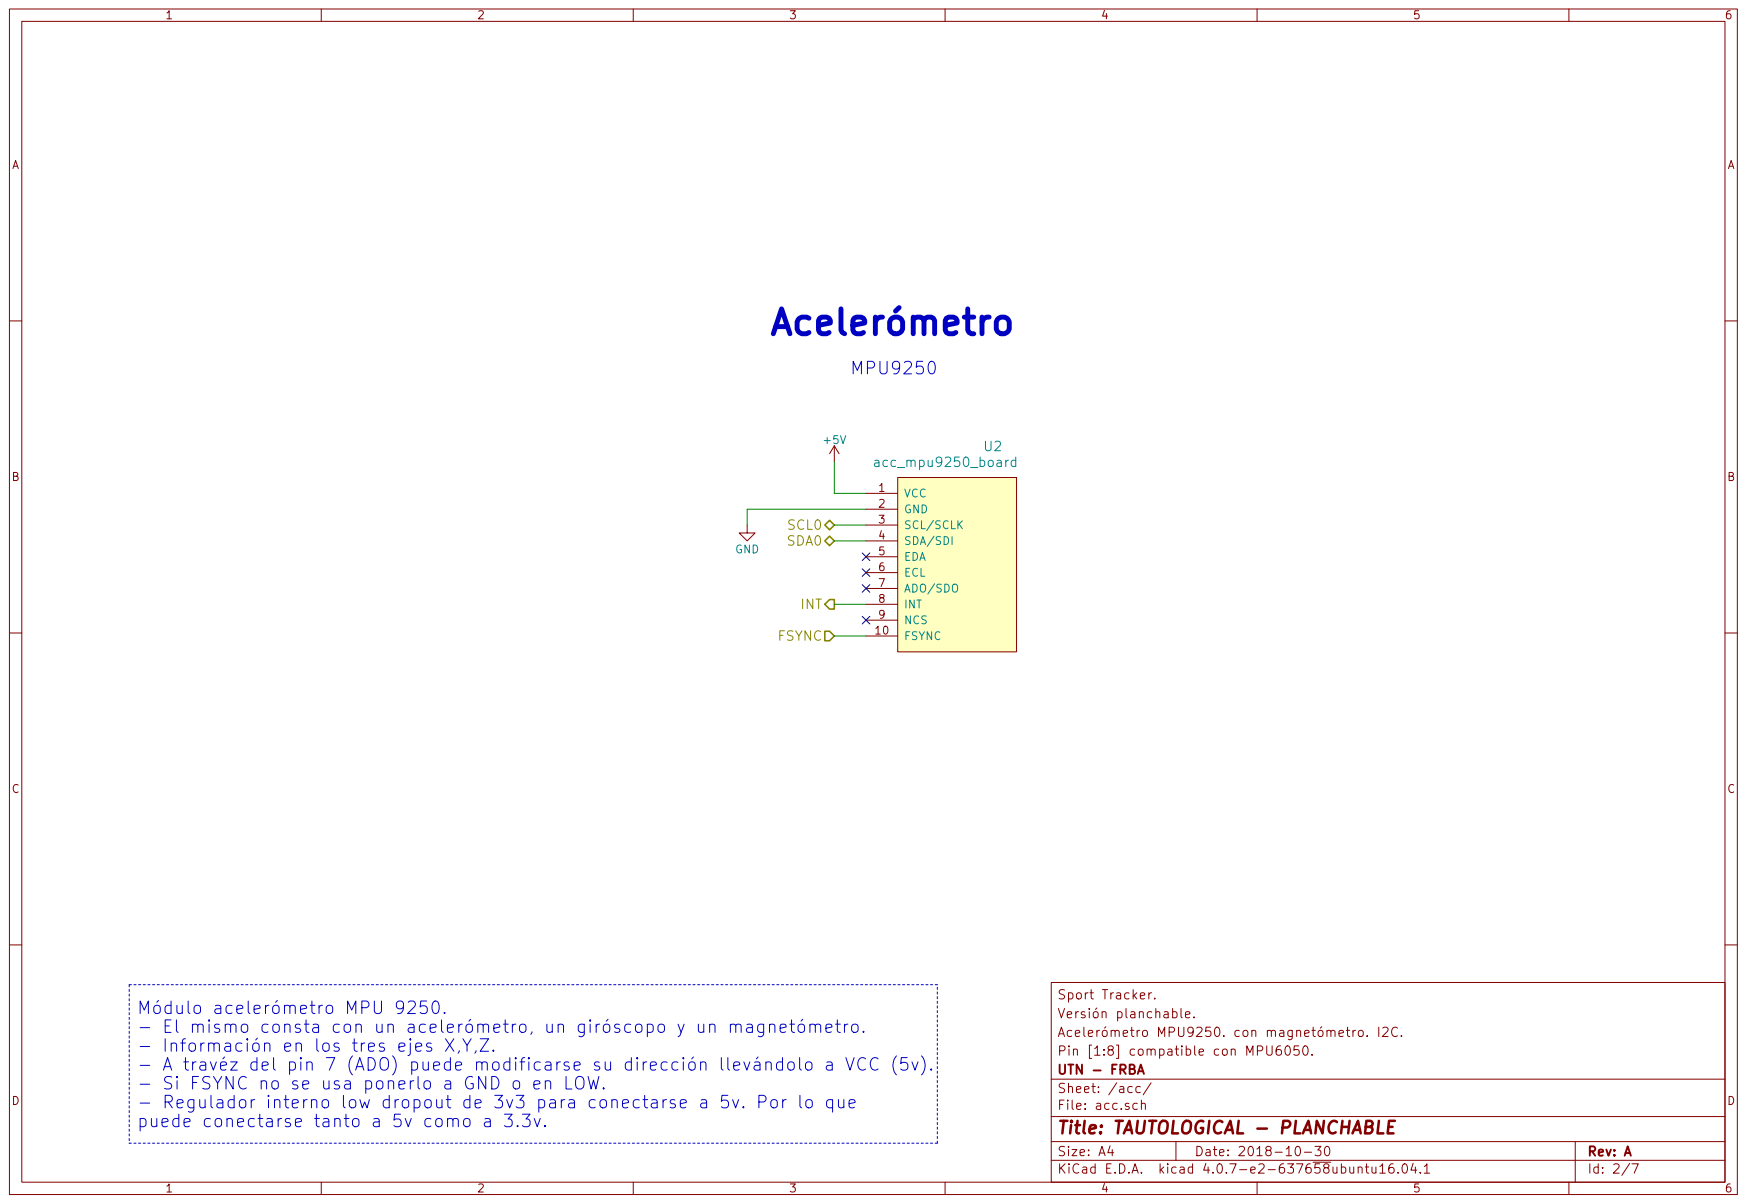
[picture p67: page 2]

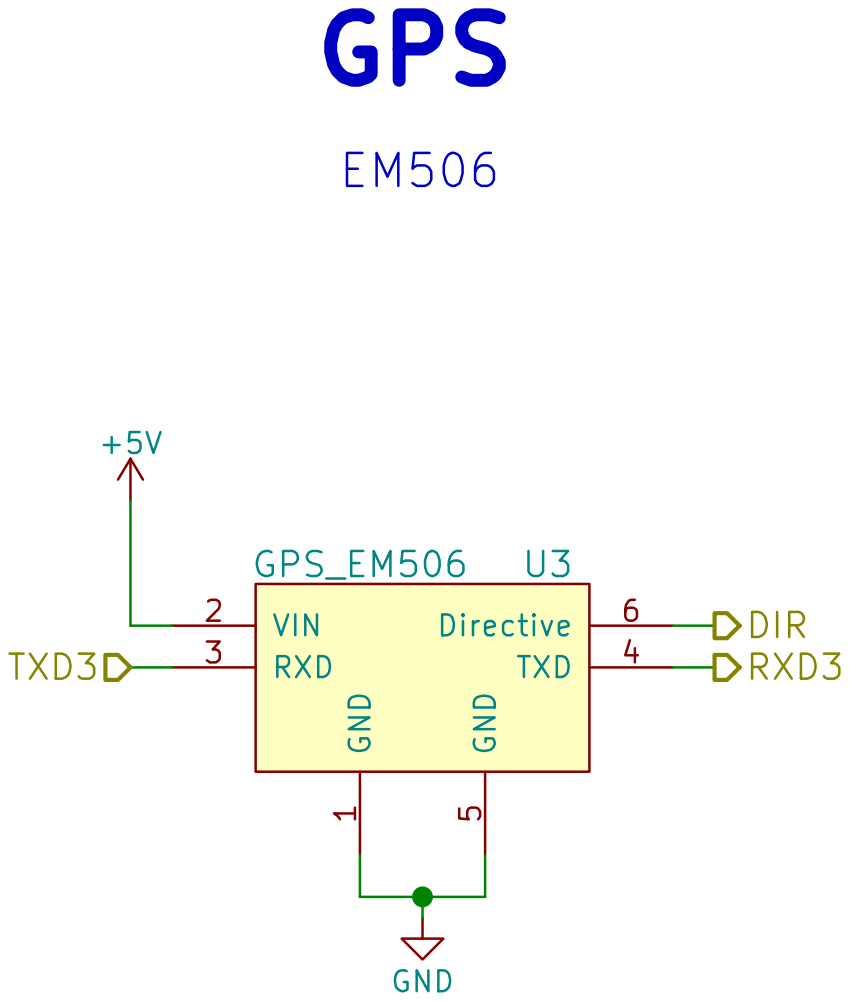
[picture p68: page 3]

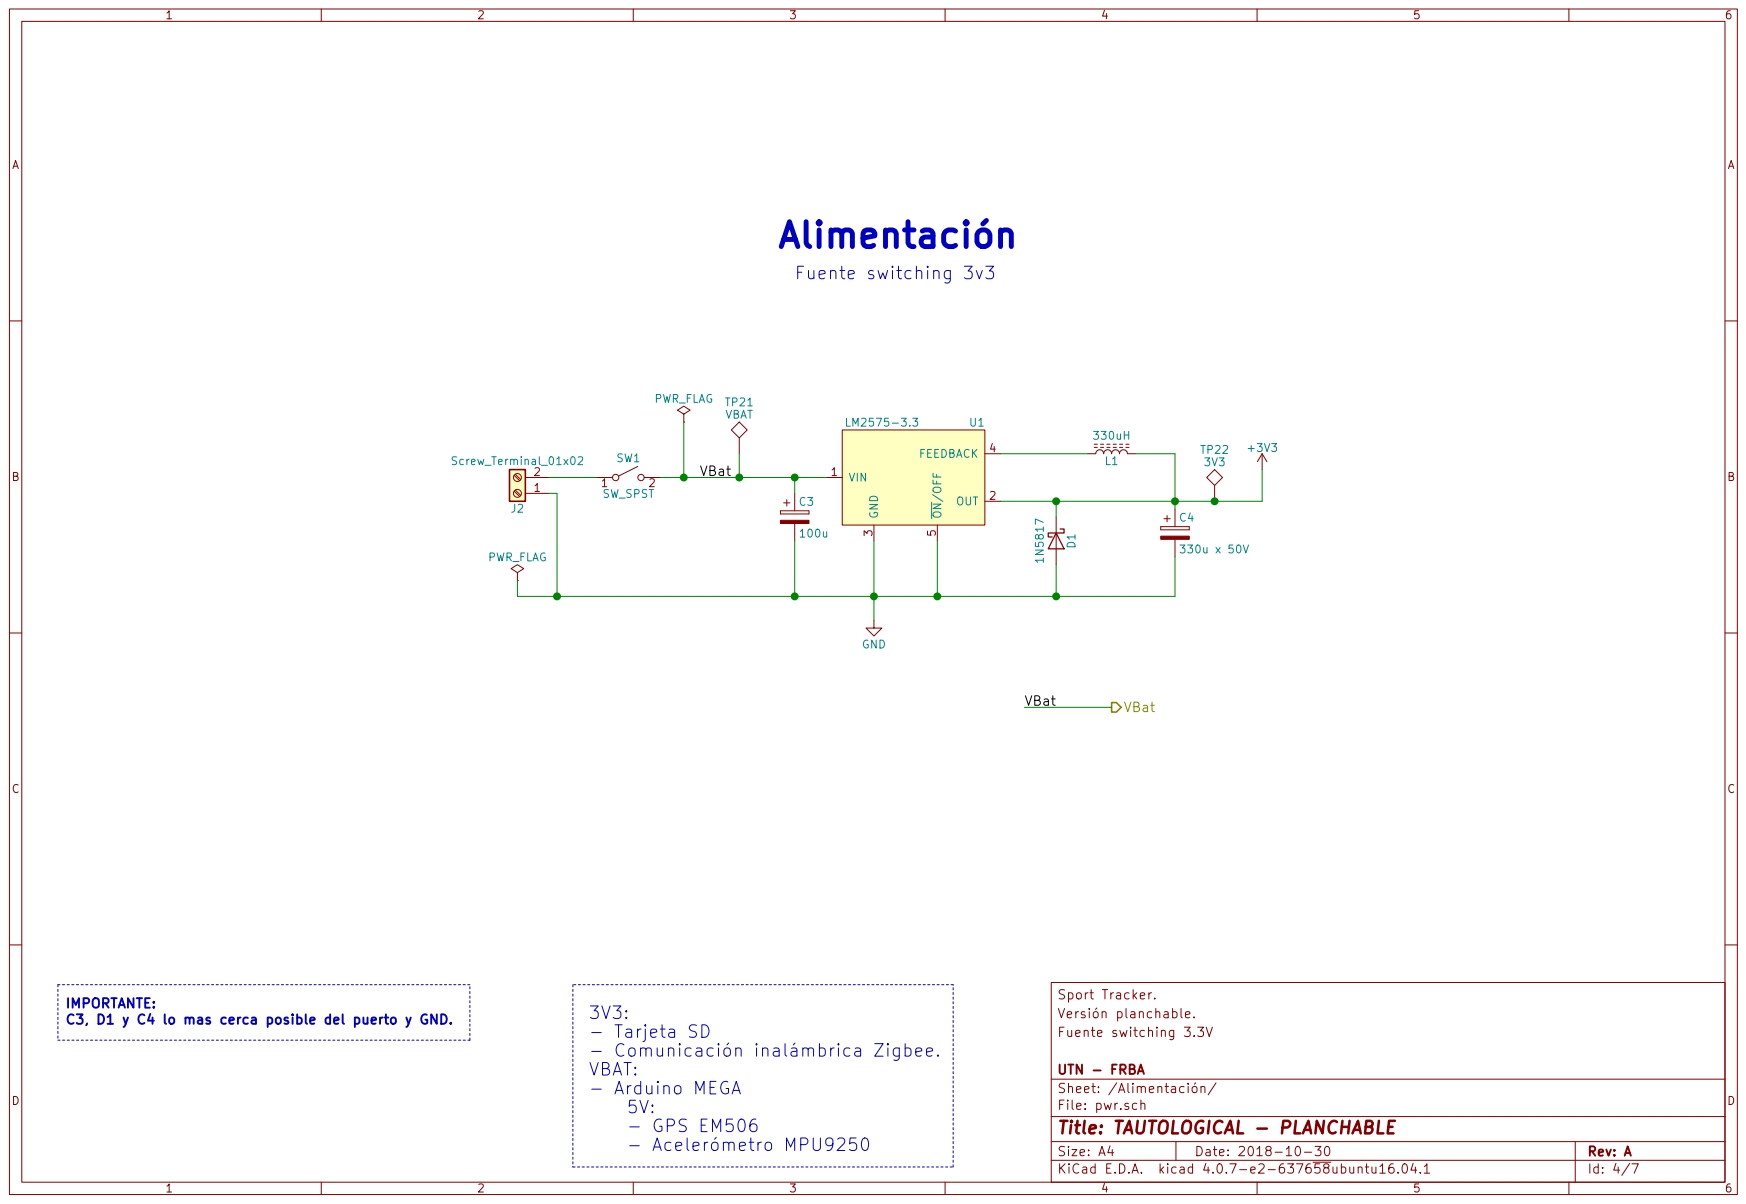
[picture p69: page 4]

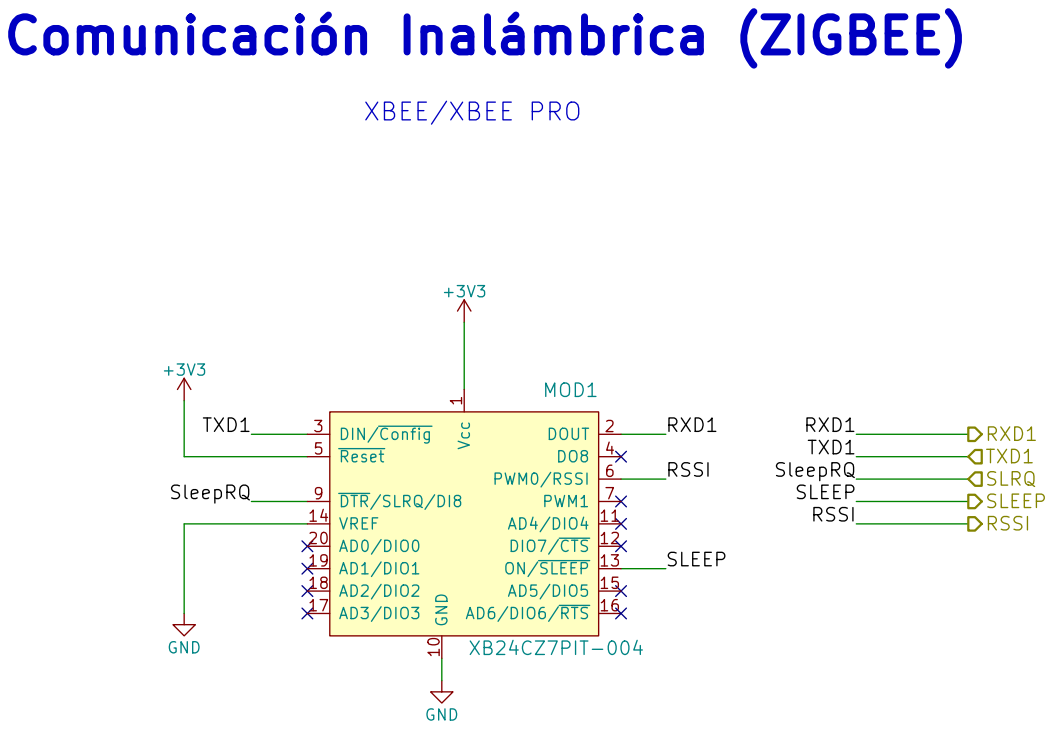
[picture p70: page 5]

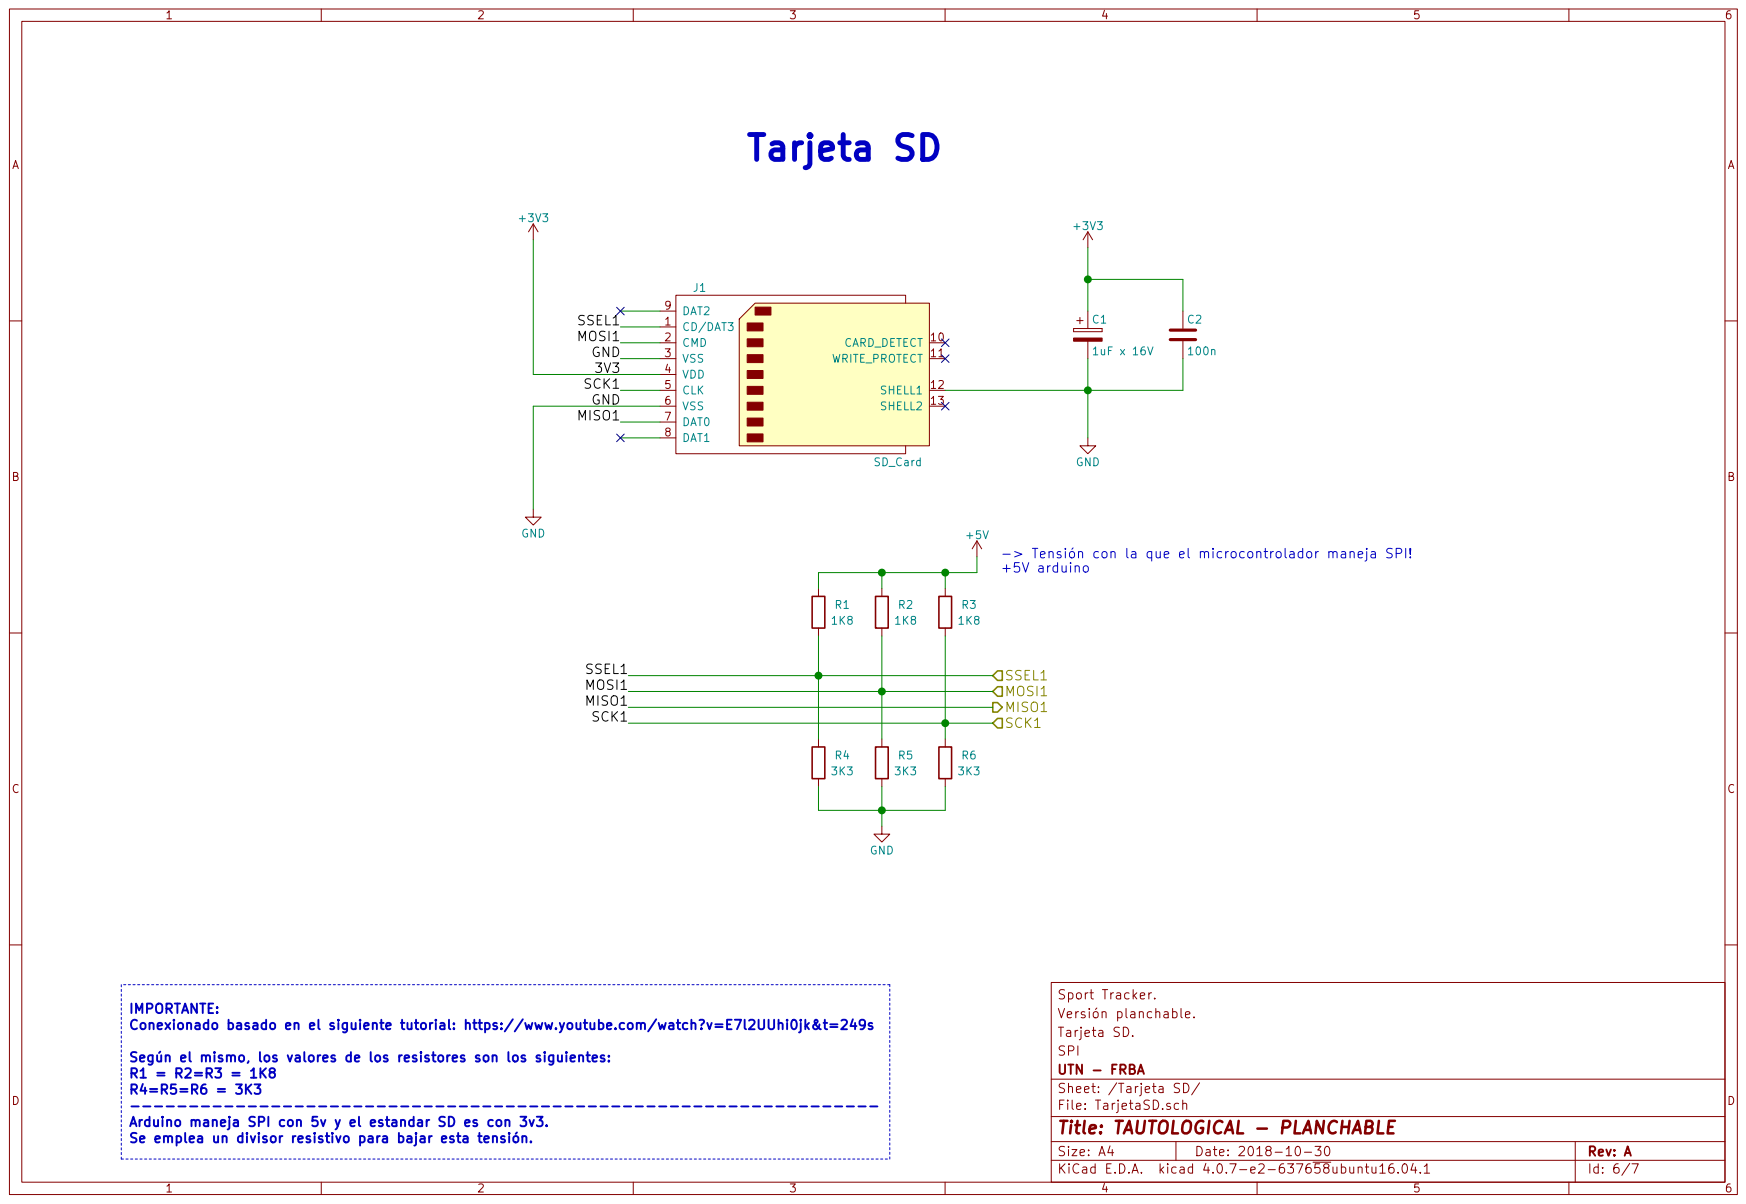
[picture p71: page 6]

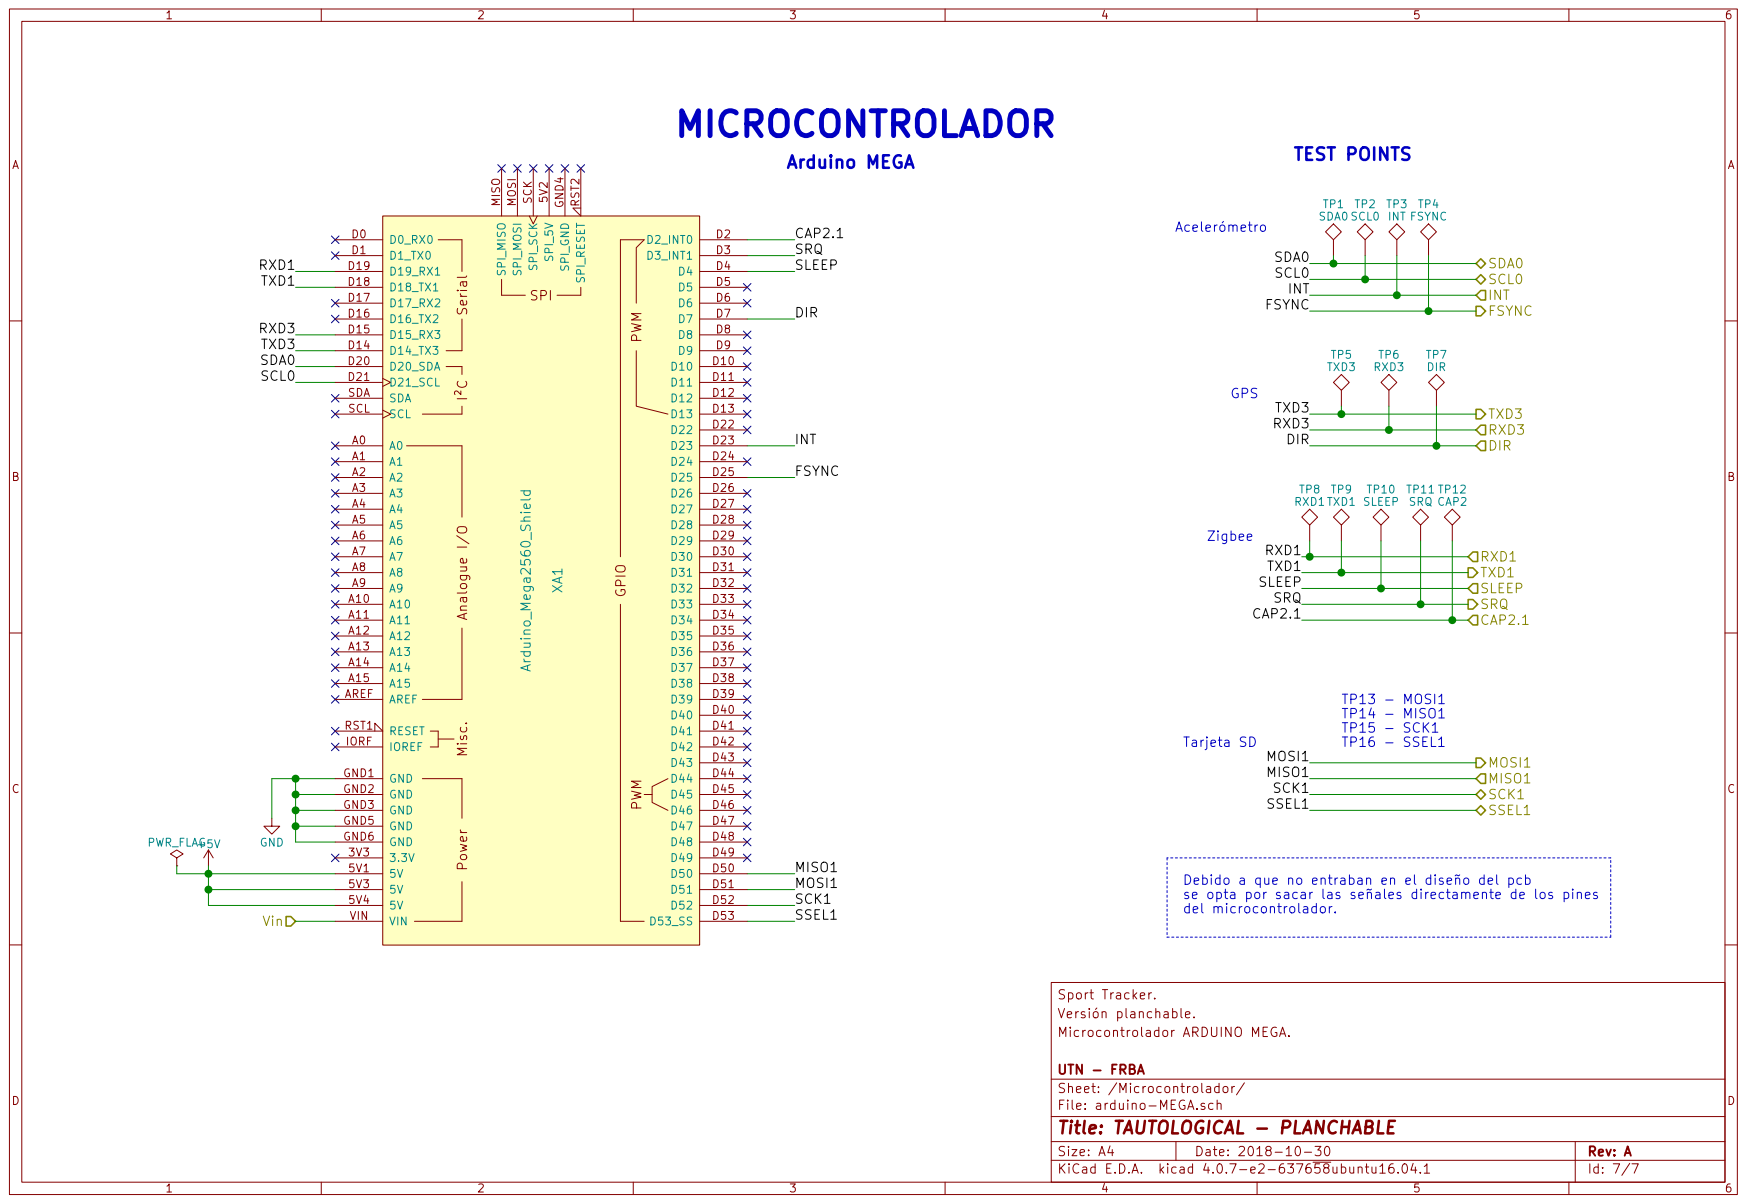
[picture p72: page 7]
